VCHSRobots/EpicFMS/cad/MovingTarget/M21-MT-0001.SLDASM

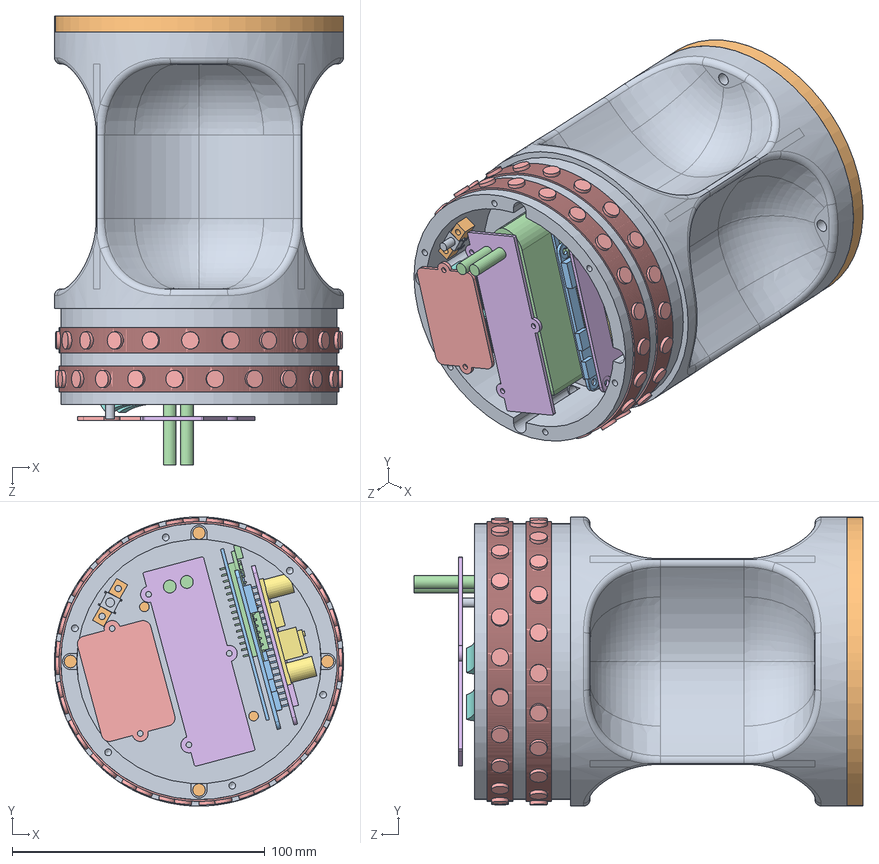
[picture p43: CAD file, 2021-10-06]
cad/MovingTarget/M21-MT-0001.SLDASM
114.4 x 114.3 x 177.5 mm
M21-MT-3002
M21-MT-3003
LipoBattery_1500mah_2S__Amazon
NeopixelRingSLDPRT x 2
M21-MT-7002
DCtoDC_Convertor_2Amp
RockerSwitch x 2
MicroPushButton
M21-MT-3006
ElegooBoard_Thin
ESP8266
