VCHSRobots/EpicFMS/cad/MovingTarget/M21-MT-0002.SLDASM

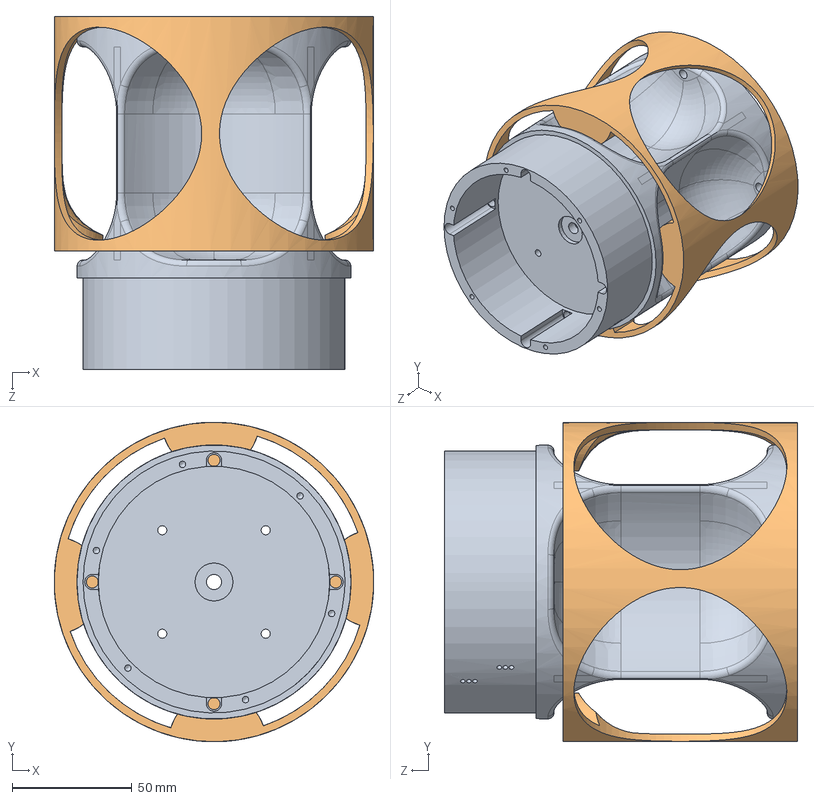
[picture p44: CAD file, 2021-10-06]
cad/MovingTarget/M21-MT-0002.SLDASM
133.3 x 133.3 x 147.3 mm
M21-MT-3002
M21-MT-3005
