VCHSRobots/EpicFMS/cad/CamerRingLEDs/M21-GP-3013.SLDPRT

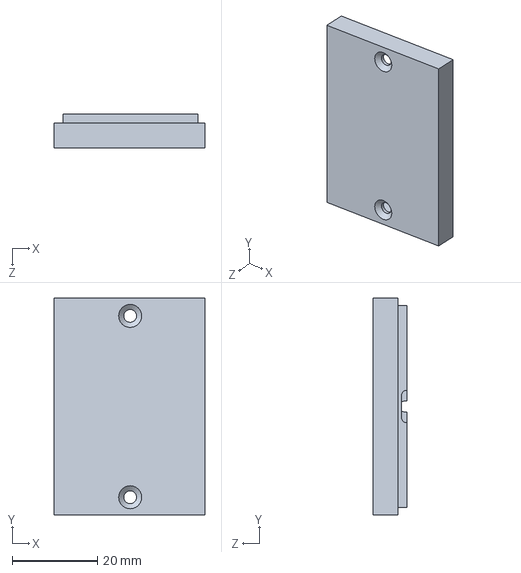
[picture p45: CAD file, 2021-11-01]
cad/CamerRingLEDs/M21-GP-3013.SLDPRT
35.2 x 50.8 x 7.87 mm
