VCHSRobots/EpicFMS/cad/DocTrash/TargetBoardForDiagram.SLDPRT

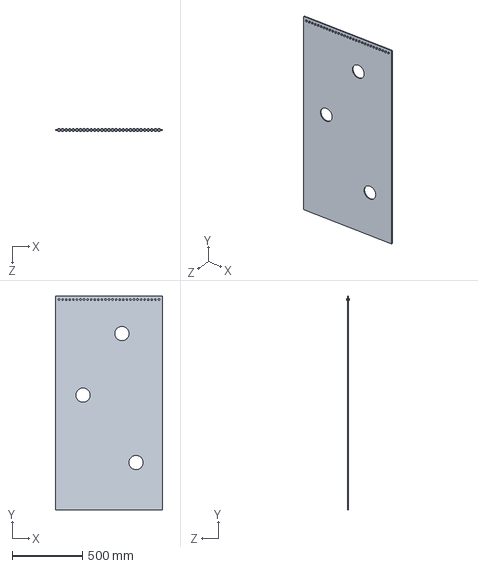
[picture p46: CAD file, 2021-10-06]
cad/DocTrash/TargetBoardForDiagram.SLDPRT
762.0 x 1524.0 x 19.0 mm
