VCHSRobots/EpicFMS/cad/DoorSliderTarget/M21-SL-3012.SLDPRT

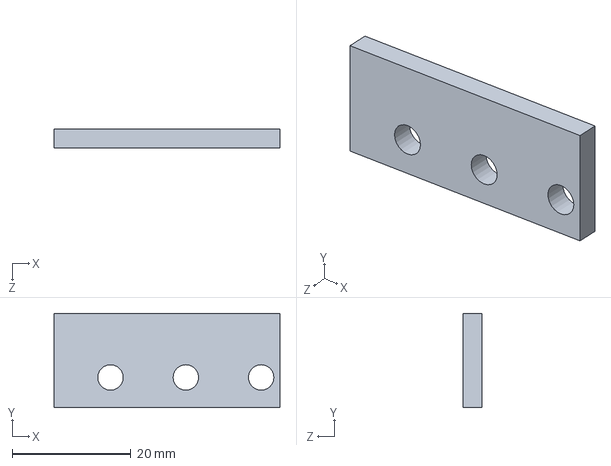
[picture p47: CAD file, 2021-10-22]
cad/DoorSliderTarget/M21-SL-3012.SLDPRT
38.1 x 15.9 x 3.17 mm
