VCHSRobots/EpicFMS/cad/MovingTarget/M21-MT-3010.SLDPRT

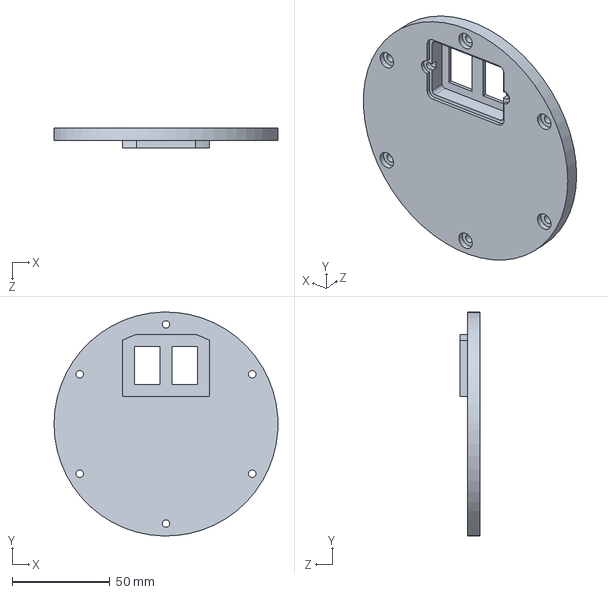
[picture p48: CAD file, 2021-10-29]
cad/MovingTarget/M21-MT-3010.SLDPRT
114.3 x 114.2 x 10.2 mm
