VCHSRobots/EpicFMS/cad/SupplierLib/DCtoDC_Convertor_eBoot_Mini_MP1584EN_Amazon.SLDPRT

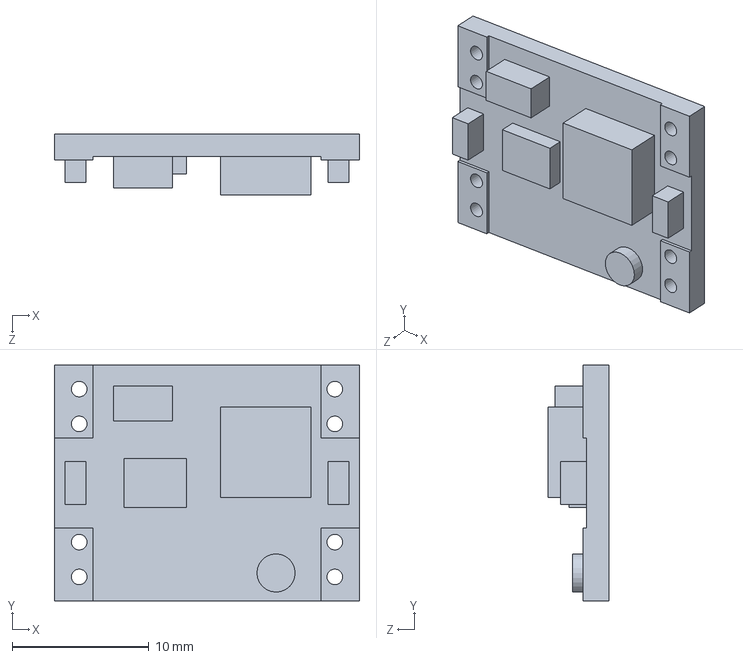
[picture p49: CAD file, 2021-11-01]
cad/SupplierLib/DCtoDC_Convertor_eBoot_Mini_MP1584EN_Amazon.SLDPRT
22.3 x 17.2 x 4.42 mm
