VCHSRobots/EpicFMS/cad/TestJigs/M21-GP-3002.SLDPRT

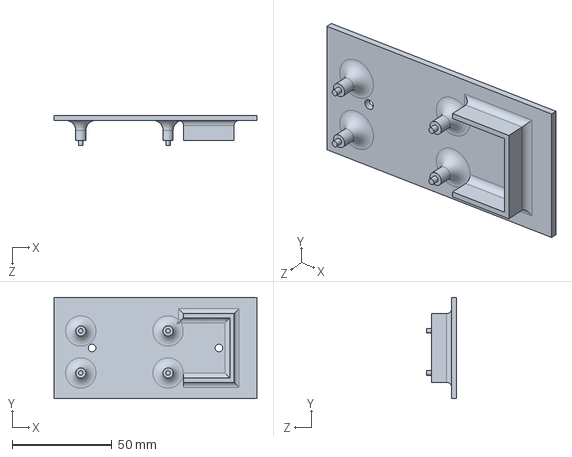
[picture p50: CAD file, 2021-10-07]
cad/TestJigs/M21-GP-3002.SLDPRT
101.6 x 50.8 x 15.2 mm
