VCHSRobots/EpicFMS/cad/BasketTarget/M21-HG-3004.SLDPRT

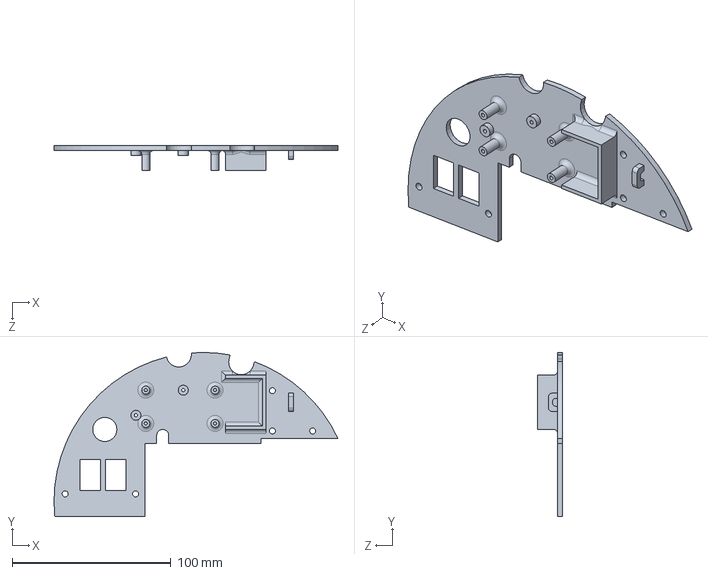
[picture p51: CAD file, 2021-10-07]
cad/BasketTarget/M21-HG-3004.SLDPRT
179.2 x 103.5 x 15.9 mm
