VCHSRobots/EpicFMS/cad/DocTrash/BasketForDiagram.SLDPRT

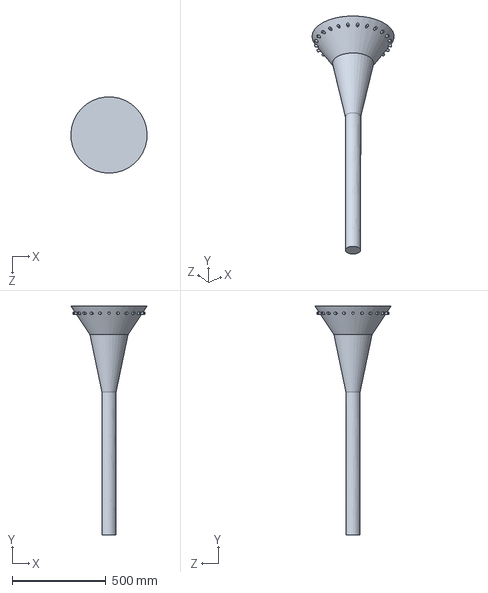
[picture p52: CAD file, 2021-10-06]
cad/DocTrash/BasketForDiagram.SLDPRT
406.0 x 1219.2 x 406.4 mm
