VCHSRobots/EpicFMS/cad/MovingTarget/M21-MT-3011.SLDPRT

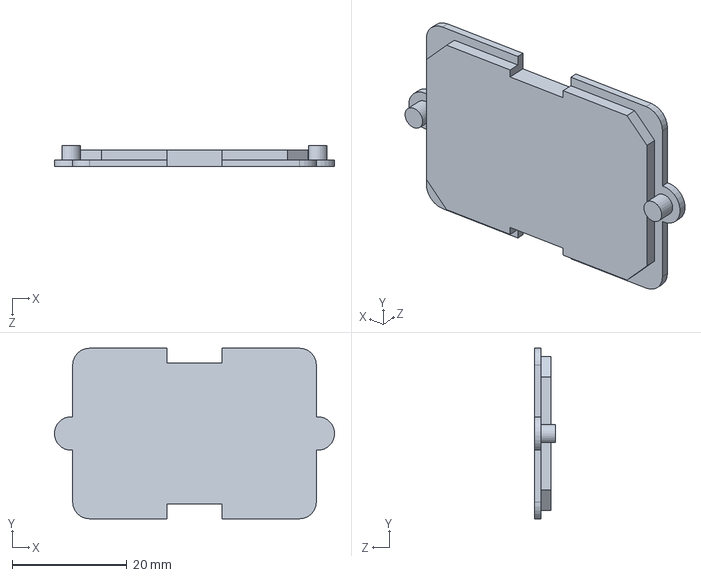
[picture p53: CAD file, 2021-10-29]
cad/MovingTarget/M21-MT-3011.SLDPRT
48.7 x 29.7 x 3.70 mm
