VCHSRobots/EpicFMS/cad/PCB_Models/M21-GP-7003.SLDPRT

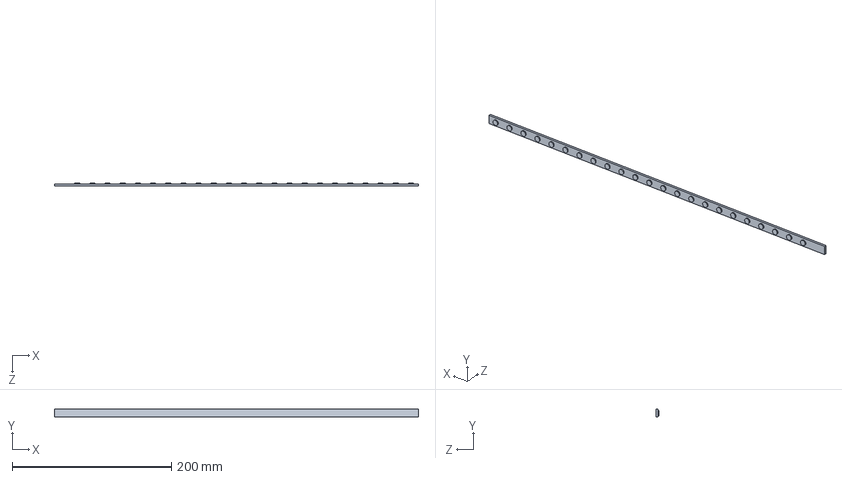
[picture p54: CAD file, 2021-10-09]
cad/PCB_Models/M21-GP-7003.SLDPRT
457.2 x 10.2 x 3.81 mm
