VCHSRobots/EpicFMS/cad/PowerSupplyBox/M21-GP-3008.SLDPRT

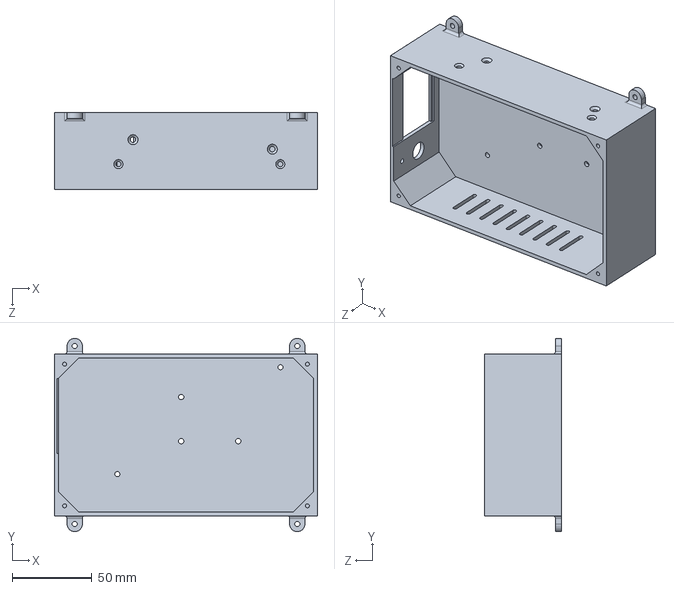
[picture p55: CAD file, 2021-10-20]
cad/PowerSupplyBox/M21-GP-3008.SLDPRT
165.1 x 121.4 x 48.3 mm
