VCHSRobots/EpicFMS/cad/SupplierLib/LipoBattery_1000mah_2S_Amazon.SLDPRT

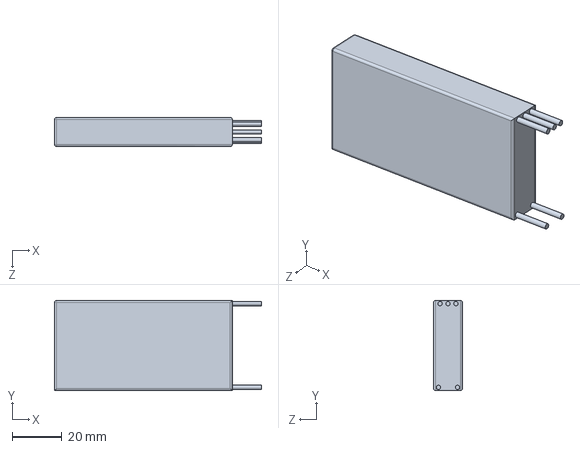
[picture p56: CAD file, 2021-10-27]
cad/SupplierLib/LipoBattery_1000mah_2S_Amazon.SLDPRT
82.8 x 36.1 x 11.7 mm
