VCHSRobots/EpicFMS/cad/TestJigs/M21-SL-3008.SLDPRT

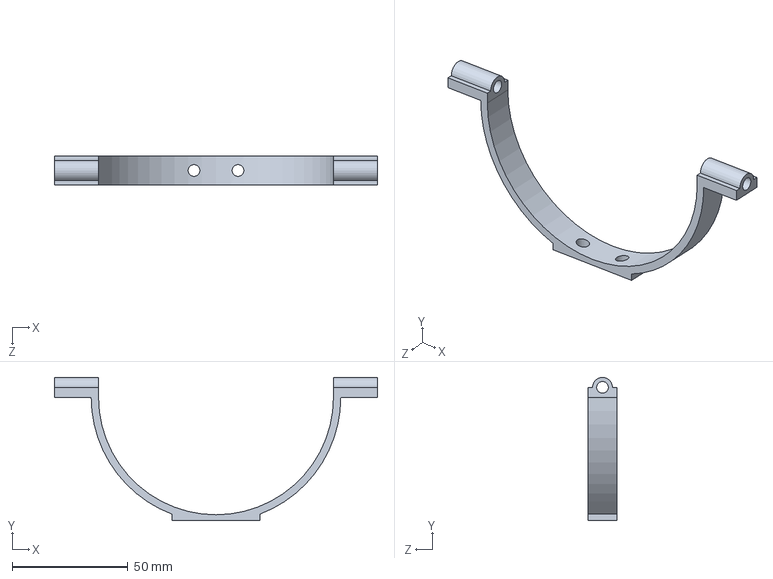
[picture p57: CAD file, 2021-10-06]
cad/TestJigs/M21-SL-3008.SLDPRT
139.7 x 62.0 x 12.7 mm
