VCHSRobots/EpicFMS/cad/BasketTarget/M21-HG-3005.SLDPRT

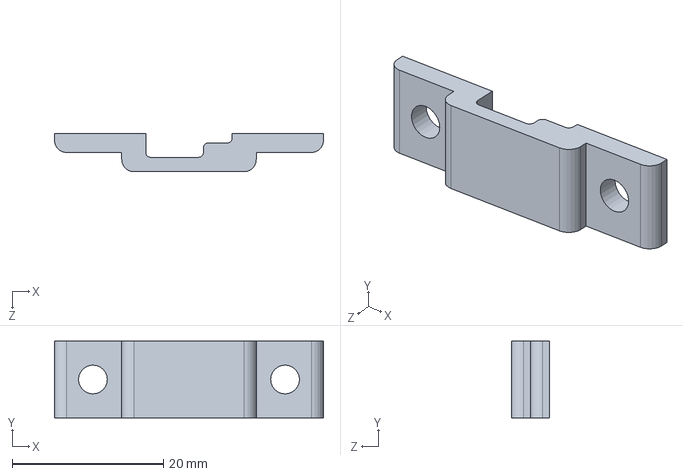
[picture p58: CAD file, 2021-10-07]
cad/BasketTarget/M21-HG-3005.SLDPRT
35.6 x 10.2 x 5.08 mm
