VCHSRobots/EpicFMS/cad/DocTrash/MovingTargetForDiagram.SLDPRT

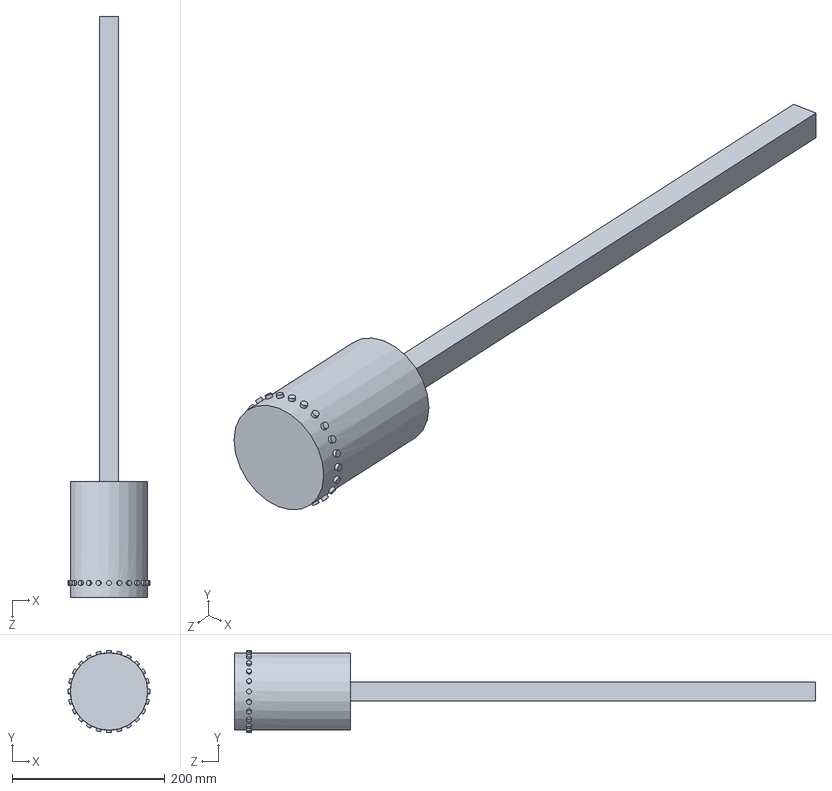
[picture p59: CAD file, 2021-10-06]
cad/DocTrash/MovingTargetForDiagram.SLDPRT
108.0 x 108.0 x 762.0 mm
