VCHSRobots/EpicFMS/cad/DoorSliderTarget/M21-SL-3009.SLDPRT

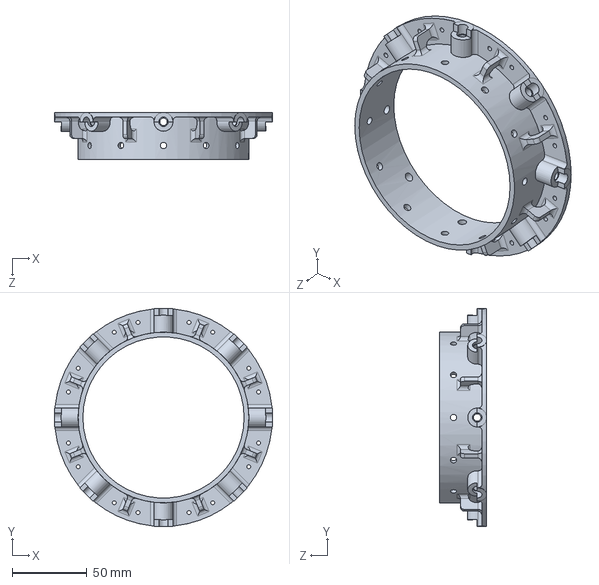
[picture p60: CAD file, 2021-10-09]
cad/DoorSliderTarget/M21-SL-3009.SLDPRT
146.2 x 146.2 x 31.8 mm
