VCHSRobots/EpicFMS/cad/PCB_Models/M21-GP-7002.SLDPRT

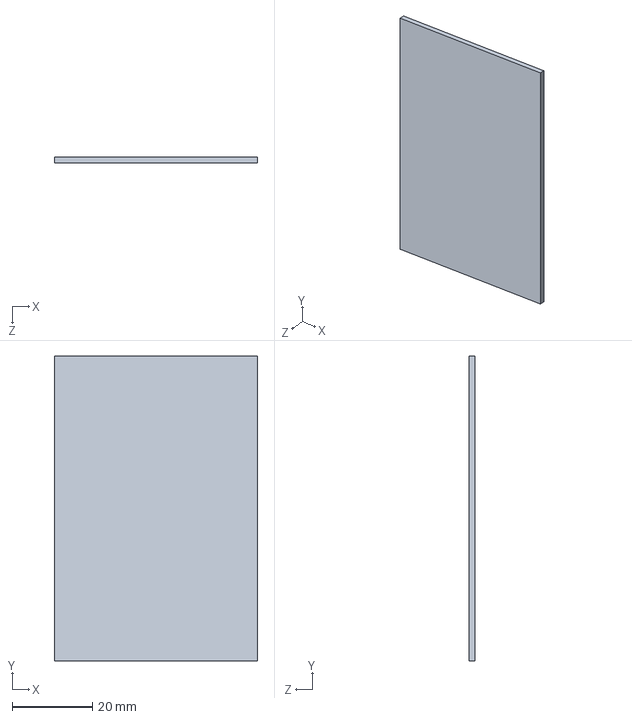
[picture p61: CAD file, 2021-10-09]
cad/PCB_Models/M21-GP-7002.SLDPRT
50.8 x 76.2 x 1.59 mm
