VCHSRobots/EpicFMS/cad/PowerSupplyBox/M21-GP-3009.SLDPRT

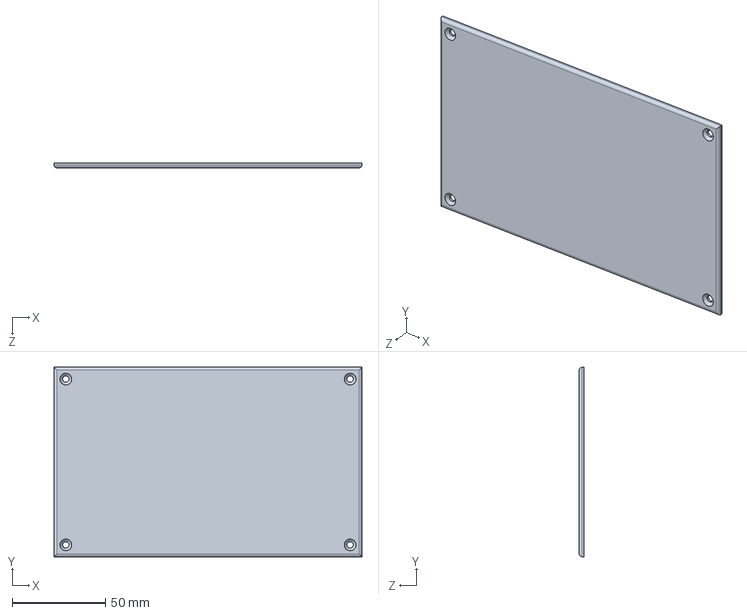
[picture p62: CAD file, 2021-10-20]
cad/PowerSupplyBox/M21-GP-3009.SLDPRT
165.1 x 101.6 x 2.54 mm
