VCHSRobots/EpicFMS/cad/SupplierLib/HeatSink_Digitkey.SLDPRT

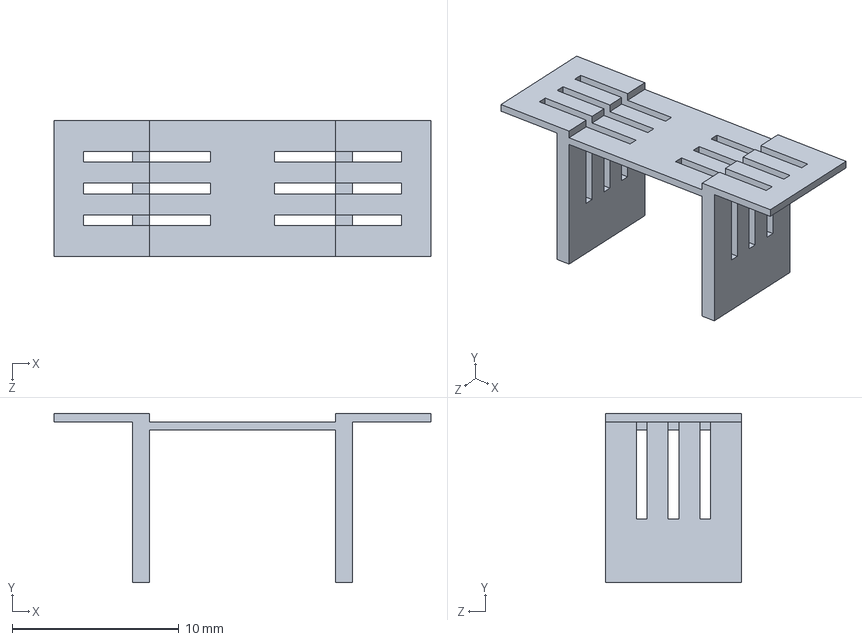
[picture p63: CAD file, 2021-10-27]
cad/SupplierLib/HeatSink_Digitkey.SLDPRT
22.6 x 10.2 x 8.13 mm
