VCHSRobots/EpicFMS/cad/TestJigs/M21-GP-3004.SLDPRT

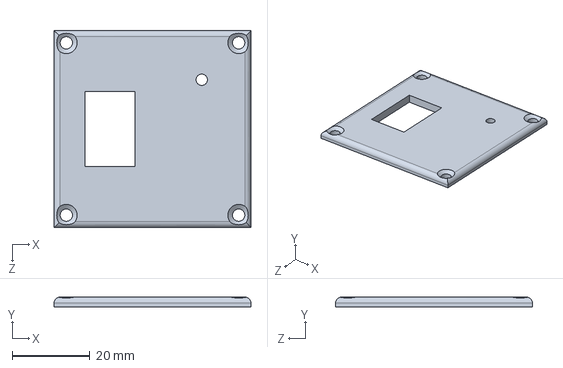
[picture p64: CAD file, 2021-10-06]
cad/TestJigs/M21-GP-3004.SLDPRT
50.8 x 2.54 x 50.8 mm
