VCHSRobots/EpicFMS/cad/BasketTarget/M21-HG-3001.SLDPRT

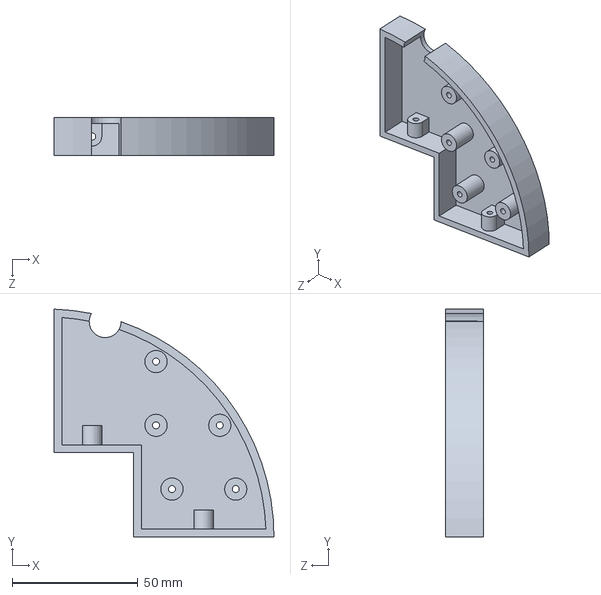
[picture p65: CAD file, 2021-10-06]
cad/BasketTarget/M21-HG-3001.SLDPRT
87.6 x 90.7 x 15.2 mm
