VCHSRobots/EpicFMS/cad/CamerRingLEDs/M21-GP-3012.SLDPRT

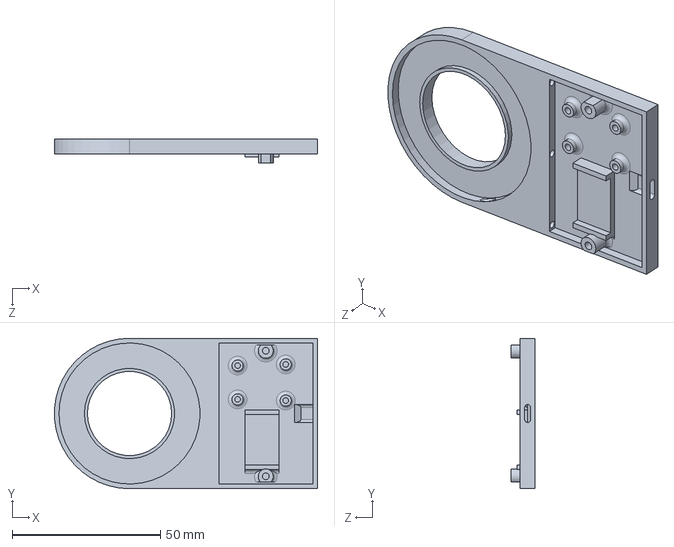
[picture p66: CAD file, 2021-11-01]
cad/CamerRingLEDs/M21-GP-3012.SLDPRT
88.8 x 50.8 x 8.26 mm
