VCHSRobots/EpicFMS/cad/DoorSliderTarget/M21-SL-3011.SLDPRT

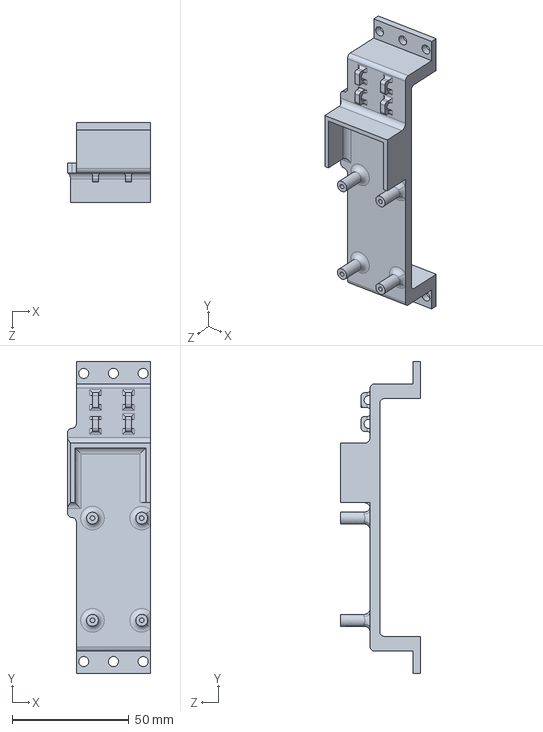
[picture p67: CAD file, 2021-10-09]
cad/DoorSliderTarget/M21-SL-3011.SLDPRT
35.6 x 133.4 x 34.3 mm
