VCHSRobots/EpicFMS/cad/SupplierLib/JST_XH_6Pin_Jack.SLDPRT

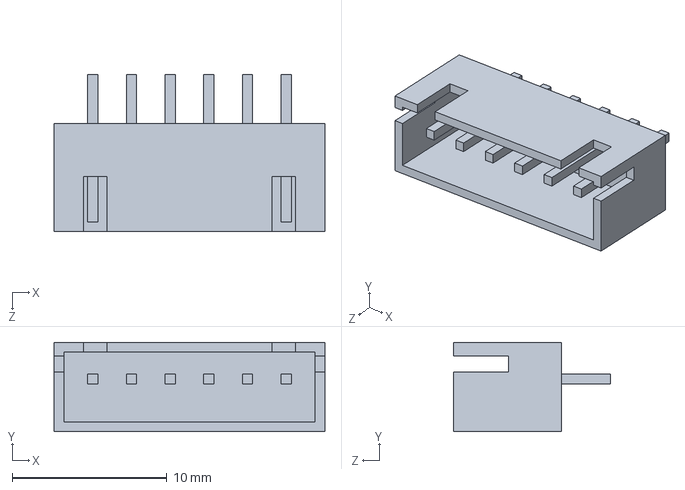
[picture p68: CAD file, 2021-10-27]
cad/SupplierLib/JST_XH_6Pin_Jack.SLDPRT
17.5 x 5.77 x 10.2 mm
