VCHSRobots/EpicFMS/cad/TestJigs/M21-GP-3003.SLDPRT

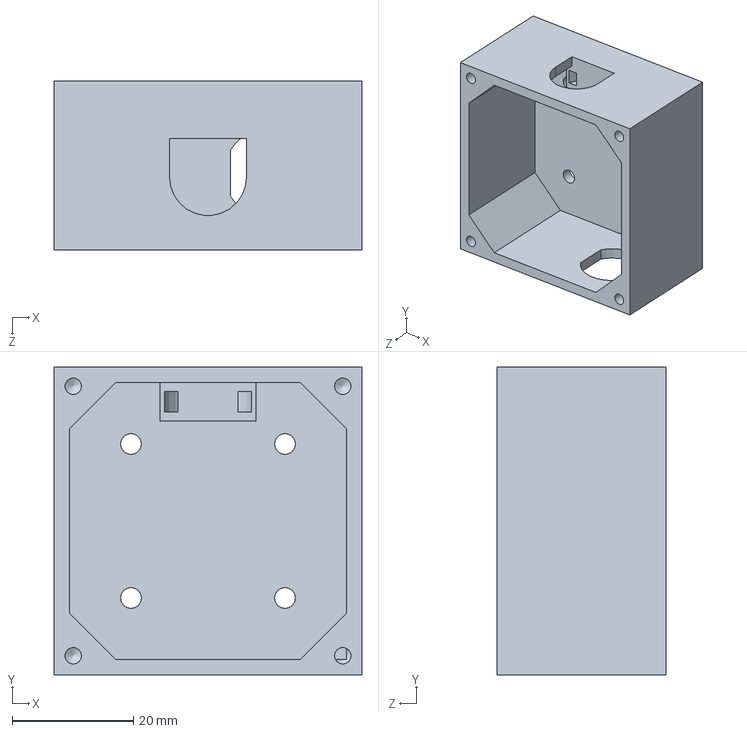
[picture p69: CAD file, 2021-10-05]
cad/TestJigs/M21-GP-3003.SLDPRT
50.8 x 50.8 x 27.9 mm
