VCHSRobots/EpicFMS/cad/BasketTarget/M21-HG-7001.SLDPRT

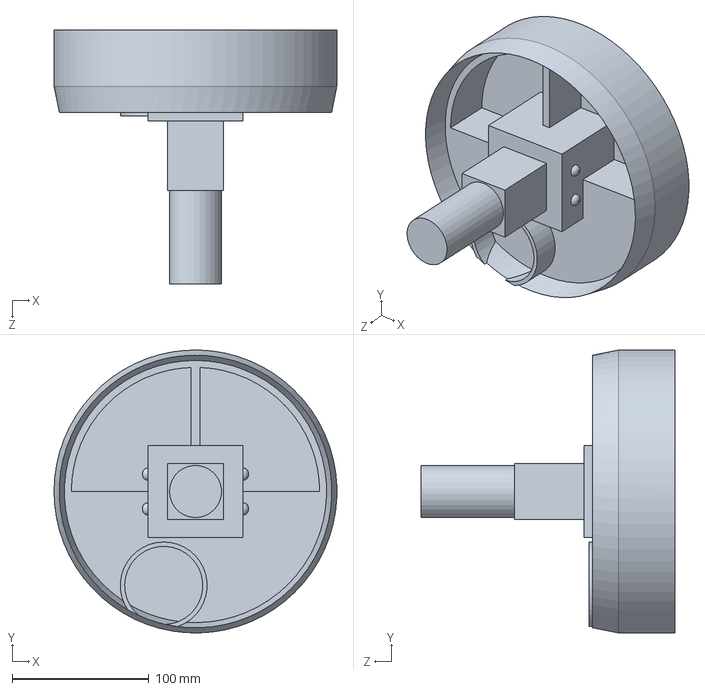
[picture p70: CAD file, 2021-10-06]
cad/BasketTarget/M21-HG-7001.SLDPRT
207.0 x 207.0 x 186.1 mm
