VCHSRobots/EpicFMS/cad/CamerRingLEDs/M21-GP-3011.SLDPRT

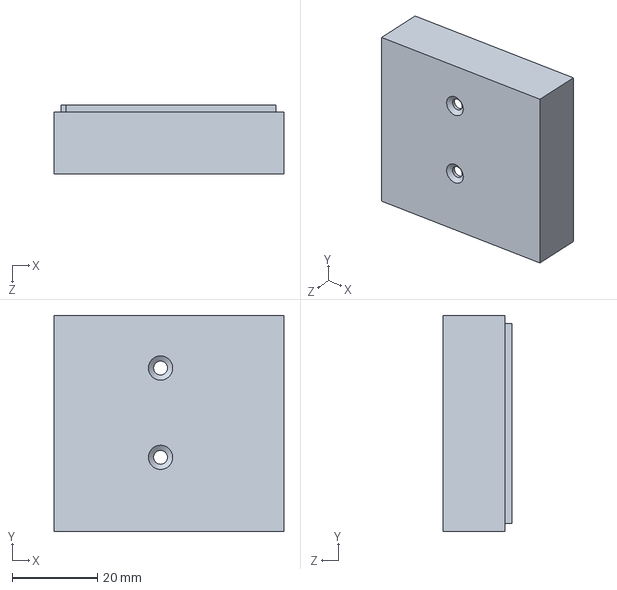
[picture p71: CAD file, 2021-10-22]
cad/CamerRingLEDs/M21-GP-3011.SLDPRT
54.0 x 50.8 x 16.2 mm
