VCHSRobots/EpicFMS/cad/DoorSliderTarget/M21-SL-3006.SLDPRT

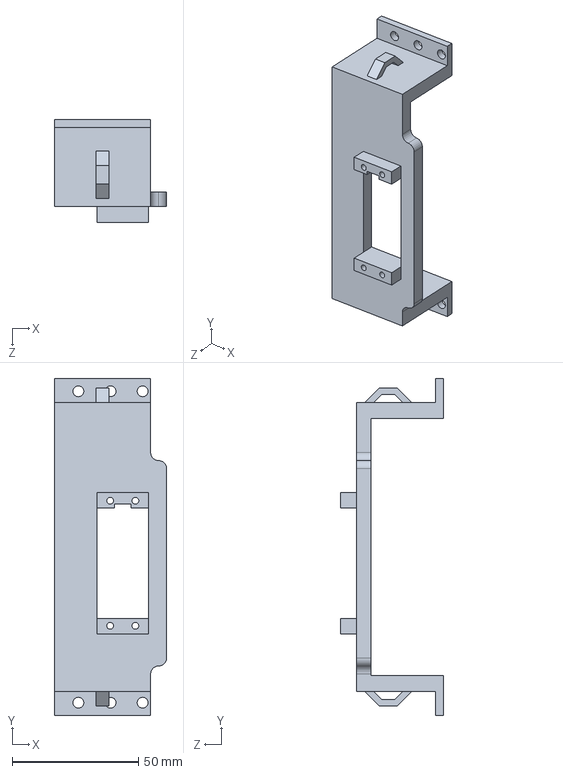
[picture p72: CAD file, 2021-10-09]
cad/DoorSliderTarget/M21-SL-3006.SLDPRT
44.4 x 133.4 x 40.6 mm
