VCHSRobots/EpicFMS/cad/MovingTarget/M21-MT-3009.SLDPRT

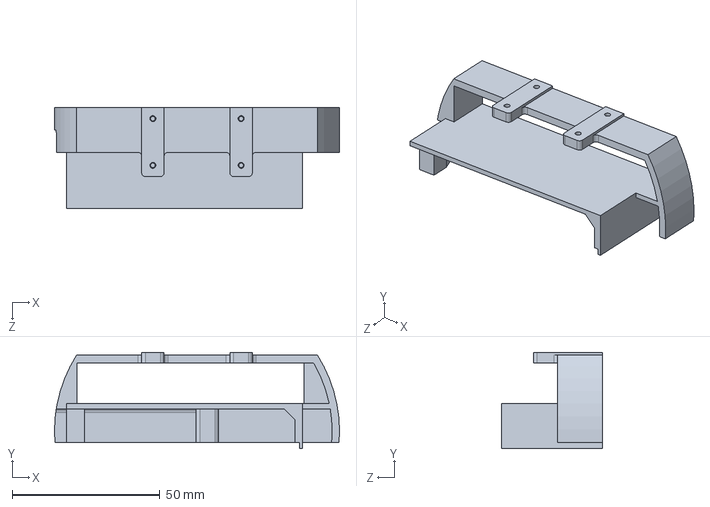
[picture p73: CAD file, 2021-10-29]
cad/MovingTarget/M21-MT-3009.SLDPRT
96.5 x 32.5 x 34.3 mm
