VCHSRobots/EpicFMS/cad/PCB_Models/M21-GP-7001.SLDPRT

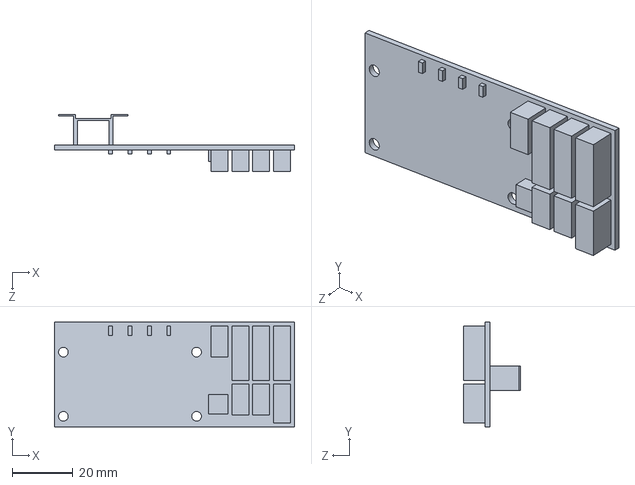
[picture p74: CAD file, 2021-10-06]
cad/PCB_Models/M21-GP-7001.SLDPRT
78.7 x 34.3 x 18.9 mm
