VCHSRobots/EpicFMS/cad/SupplierLib/JST_XH_4Pin_Jack.SLDPRT

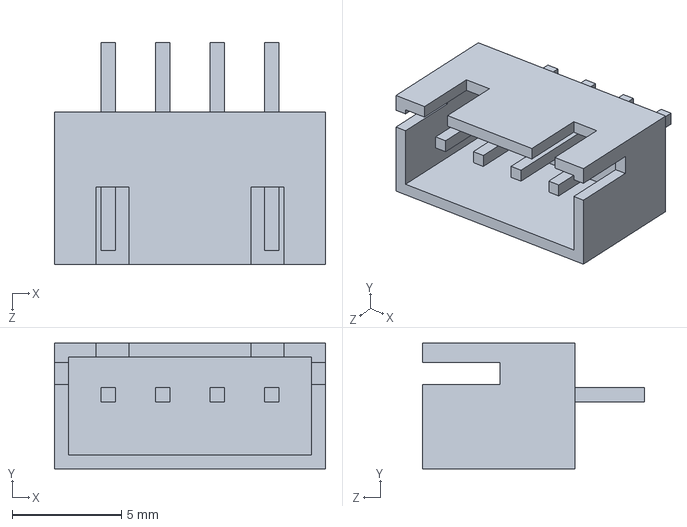
[picture p75: CAD file, 2021-10-27]
cad/SupplierLib/JST_XH_4Pin_Jack.SLDPRT
12.4 x 5.77 x 10.2 mm
