VCHSRobots/EpicFMS/cad/TestJigs/M21-GP-3007.SLDPRT

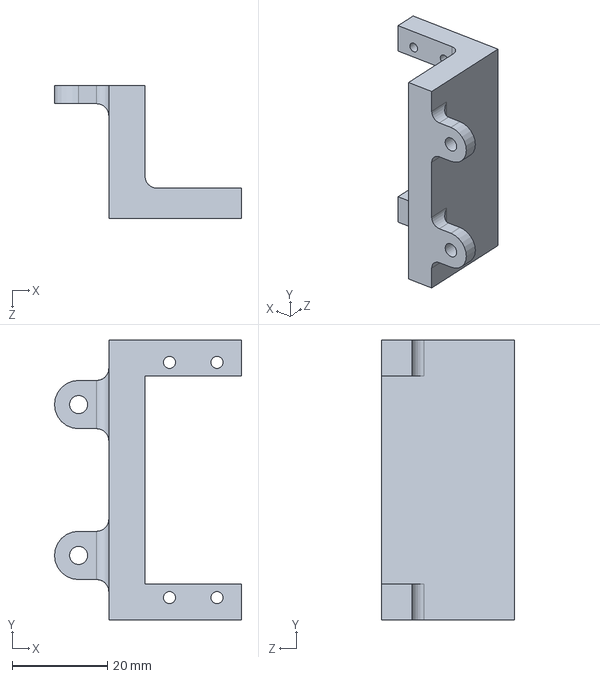
[picture p76: CAD file, 2021-10-05]
cad/TestJigs/M21-GP-3007.SLDPRT
39.4 x 58.9 x 27.9 mm
