VCHSRobots/EpicFMS/cad/BasketTarget/M21-HG-3003.SLDPRT

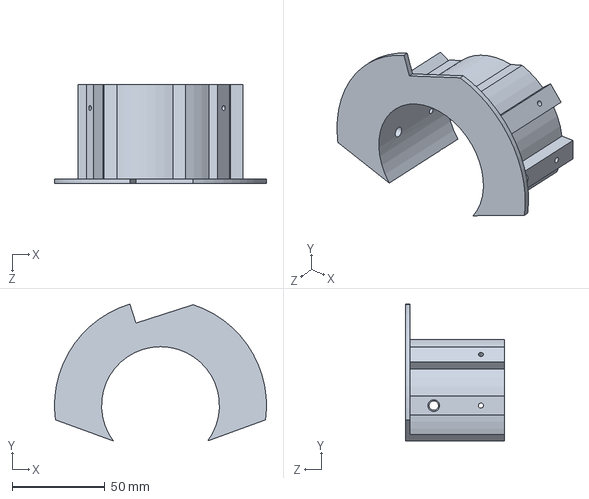
[picture p77: CAD file, 2021-10-06]
cad/BasketTarget/M21-HG-3003.SLDPRT
114.3 x 73.8 x 53.3 mm
