VCHSRobots/EpicFMS/cad/CamerRingLEDs/M21-GP-7004.SLDPRT

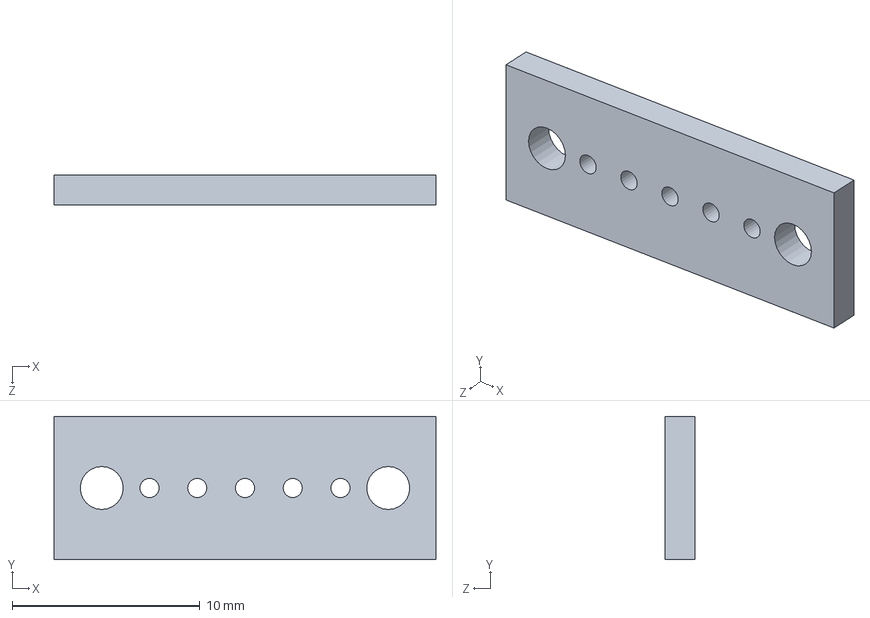
[picture p78: CAD file, 2021-10-18]
cad/CamerRingLEDs/M21-GP-7004.SLDPRT
20.3 x 7.62 x 1.59 mm
