VCHSRobots/EpicFMS/cad/DoorSliderTarget/M21-SL-6002.SLDPRT

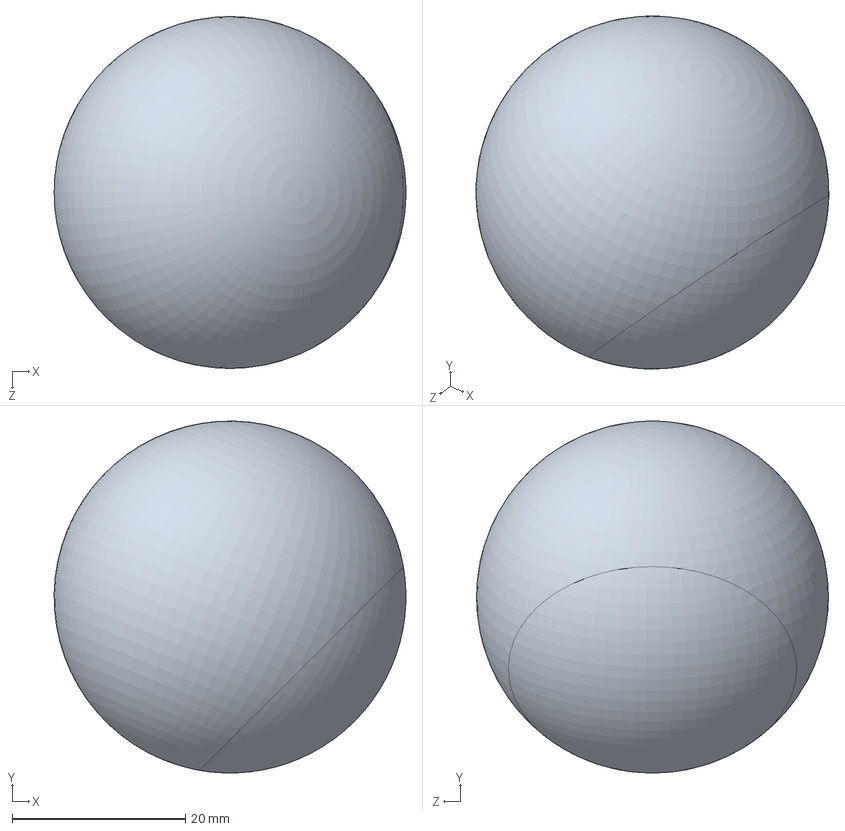
[picture p79: CAD file, 2021-10-06]
cad/DoorSliderTarget/M21-SL-6002.SLDPRT
40.6 x 40.6 x 40.6 mm
