VCHSRobots/EpicFMS/cad/SupplierLib/LED_Ring_16_Adafruit.SLDPRT

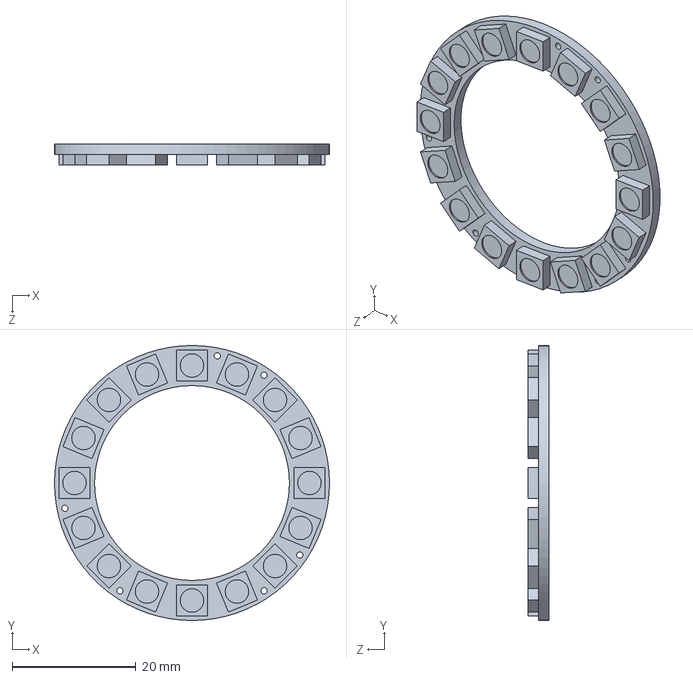
[picture p80: CAD file, 2021-10-18]
cad/SupplierLib/LED_Ring_16_Adafruit.SLDPRT
44.5 x 44.5 x 3.35 mm
