VCHSRobots/EpicFMS/cad/BasketTarget/M21-HG-7002.SLDPRT

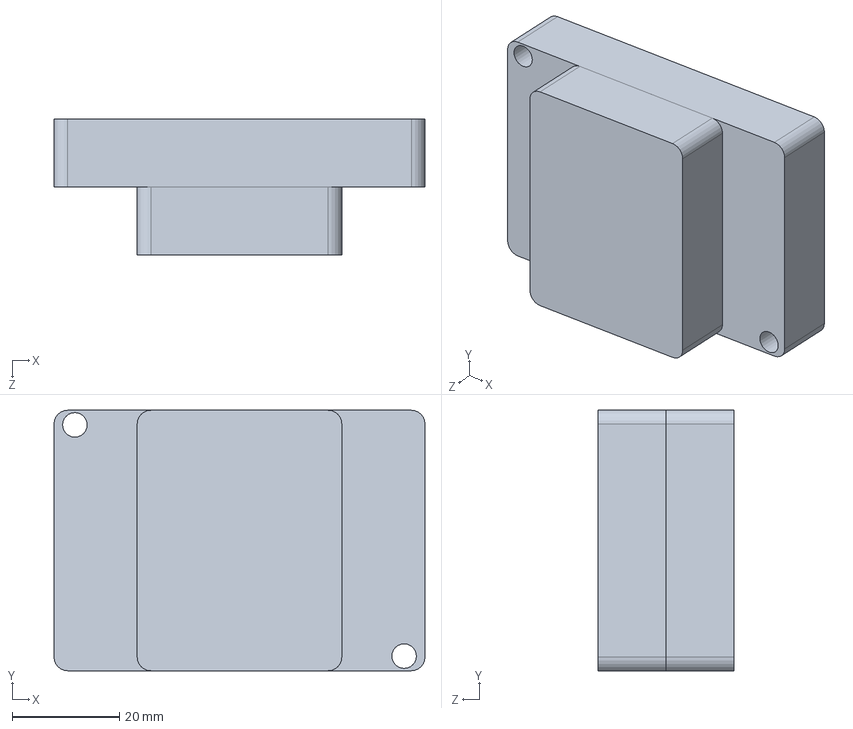
[picture p81: CAD file, 2021-10-06]
cad/BasketTarget/M21-HG-7002.SLDPRT
69.1 x 48.5 x 25.4 mm
