VCHSRobots/EpicFMS/cad/CamerRingLEDs/M21-GP-3010.SLDPRT

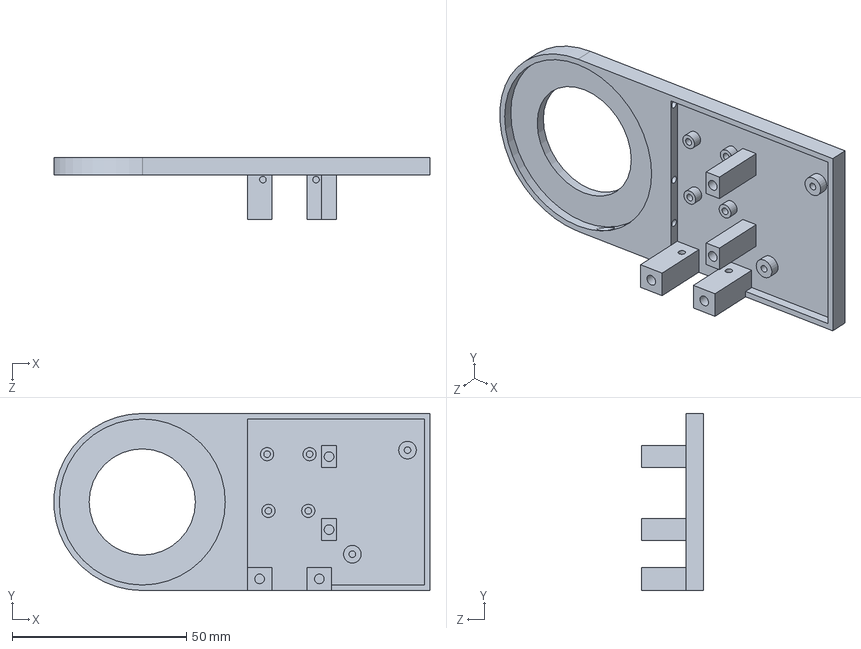
[picture p82: CAD file, 2021-10-18]
cad/CamerRingLEDs/M21-GP-3010.SLDPRT
107.9 x 50.8 x 17.8 mm
