VCHSRobots/EpicFMS/cad/SupplierLib/Trinket_M0_Adafruit.SLDPRT

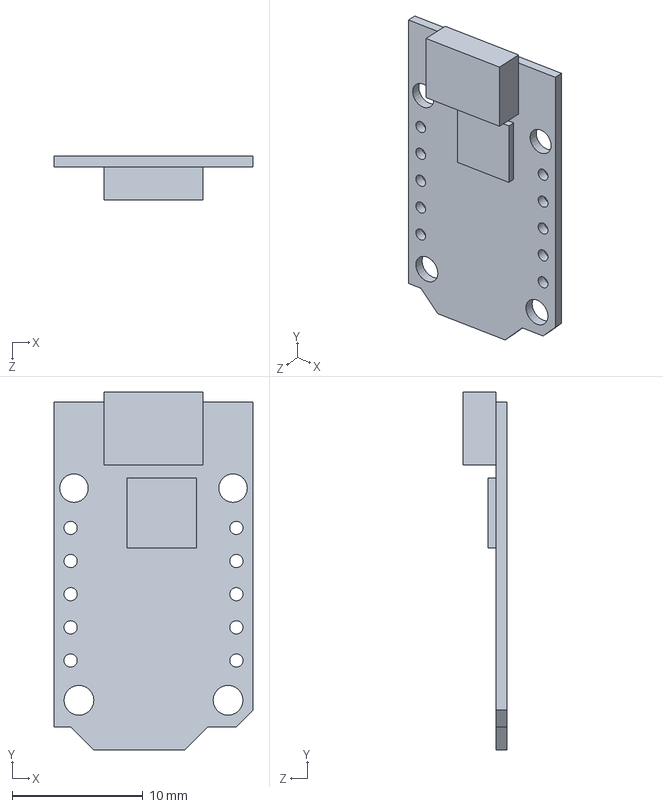
[picture p83: CAD file, 2021-10-18]
cad/SupplierLib/Trinket_M0_Adafruit.SLDPRT
15.2 x 27.4 x 3.37 mm
