VCHSRobots/EpicFMS/cad/TestJigs/M21-GP-3001.SLDPRT

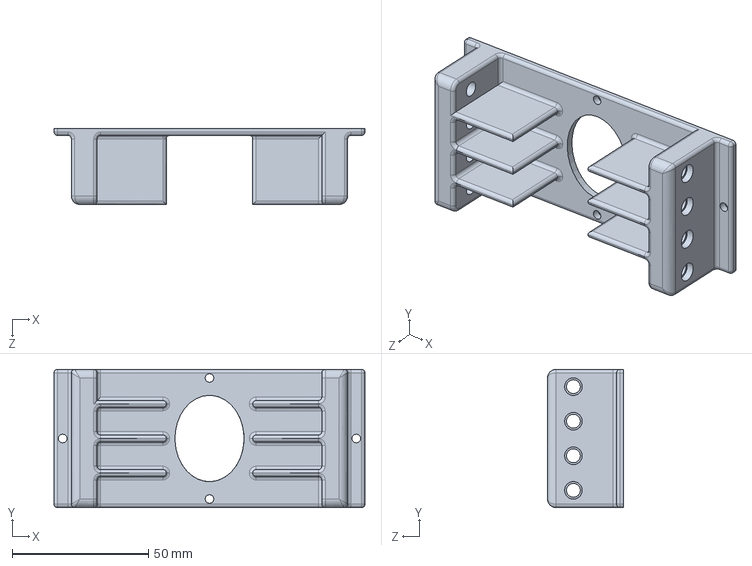
[picture p84: CAD file, 2021-10-05]
cad/TestJigs/M21-GP-3001.SLDPRT
114.3 x 50.8 x 27.9 mm
