VCHSRobots/EpicFMS/cad/BasketTarget/M21-HG-3002.SLDPRT

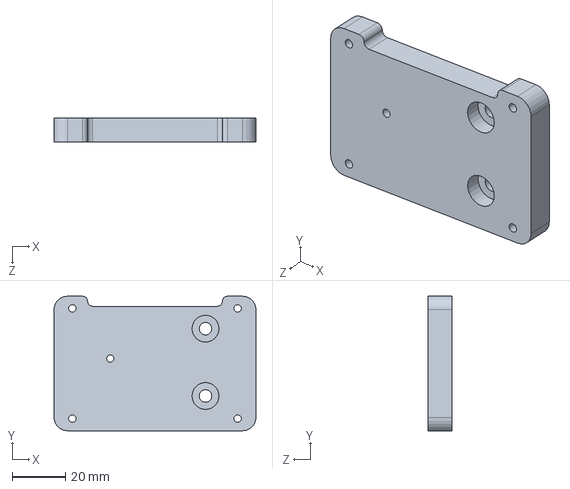
[picture p85: CAD file, 2021-10-06]
cad/BasketTarget/M21-HG-3002.SLDPRT
76.2 x 50.8 x 8.89 mm
