VCHSRobots/EpicFMS/cad/MovingTarget/M21-MT-7003.SLDPRT

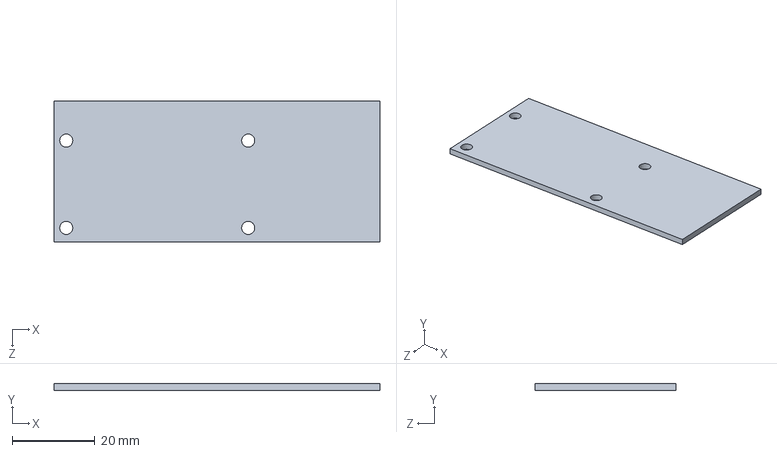
[picture p86: CAD file, 2021-10-27]
cad/MovingTarget/M21-MT-7003.SLDPRT
78.7 x 1.59 x 34.1 mm
