VCHSRobots/EpicFMS/cad/SupplierLib/JST_XH_3Pin_Jack.SLDPRT

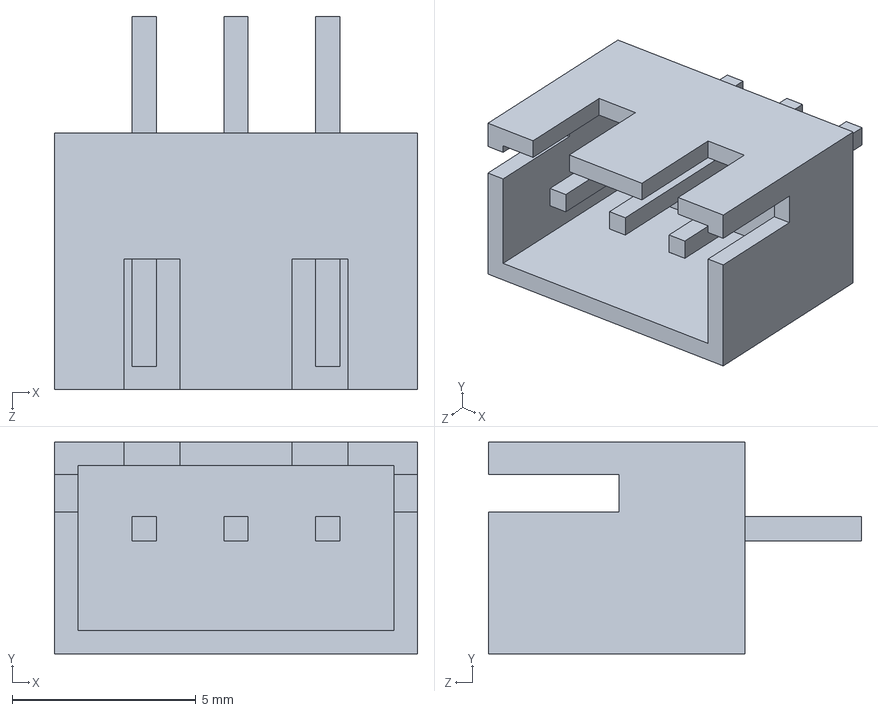
[picture p87: CAD file, 2021-10-18]
cad/SupplierLib/JST_XH_3Pin_Jack.SLDPRT
9.88 x 5.77 x 10.2 mm
