VCHSRobots/EpicFMS/cad/TestJigs/M21-GP-3005.SLDPRT

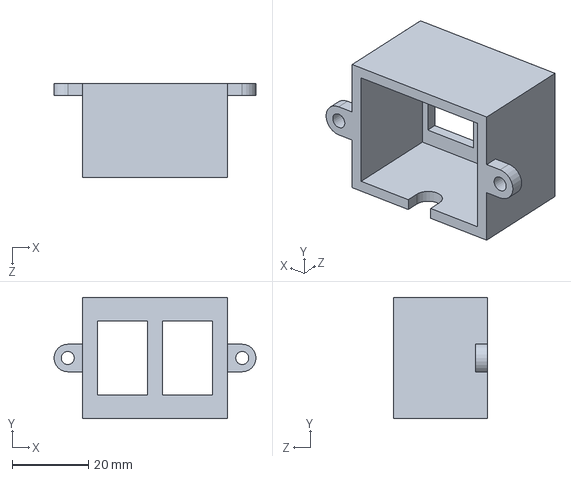
[picture p88: CAD file, 2021-10-05]
cad/TestJigs/M21-GP-3005.SLDPRT
53.0 x 31.8 x 24.8 mm
