VCHSRobots/EpicFMS/cad/DoorSliderTarget/M21-SL-3007.SLDPRT

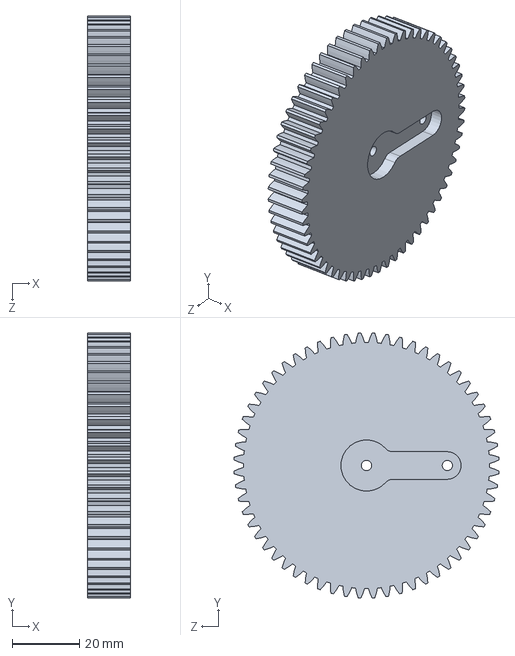
[picture p89: CAD file, 2021-10-06]
cad/DoorSliderTarget/M21-SL-3007.SLDPRT
12.7 x 78.7 x 78.7 mm
