VCHSRobots/EpicFMS/cad/MovingTarget/M21-MT-3004.SLDPRT

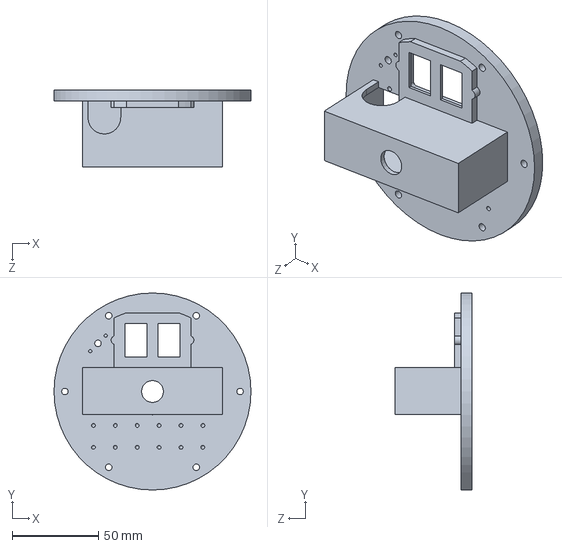
[picture p90: CAD file, 2021-10-06]
cad/MovingTarget/M21-MT-3004.SLDPRT
114.3 x 114.3 x 44.5 mm
