VCHSRobots/EpicFMS/cad/SupplierLib/AC_PowerSupply_Amazon_12v_5Amps.SLDPRT

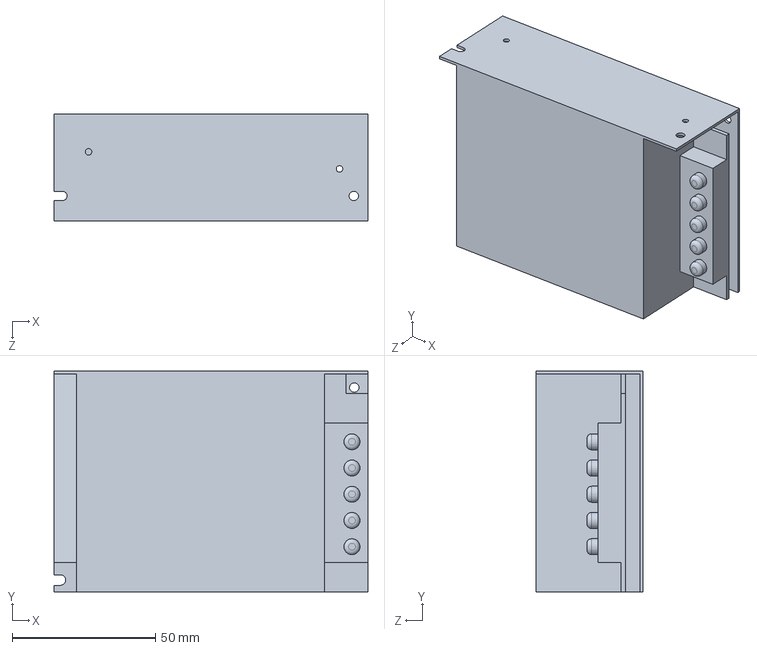
[picture p91: CAD file, 2021-10-16]
cad/SupplierLib/AC_PowerSupply_Amazon_12v_5Amps.SLDPRT
109.5 x 77.0 x 37.3 mm
