VCHSRobots/EpicFMS/cad/DoorSliderTarget/M21-SL-6001.SLDPRT

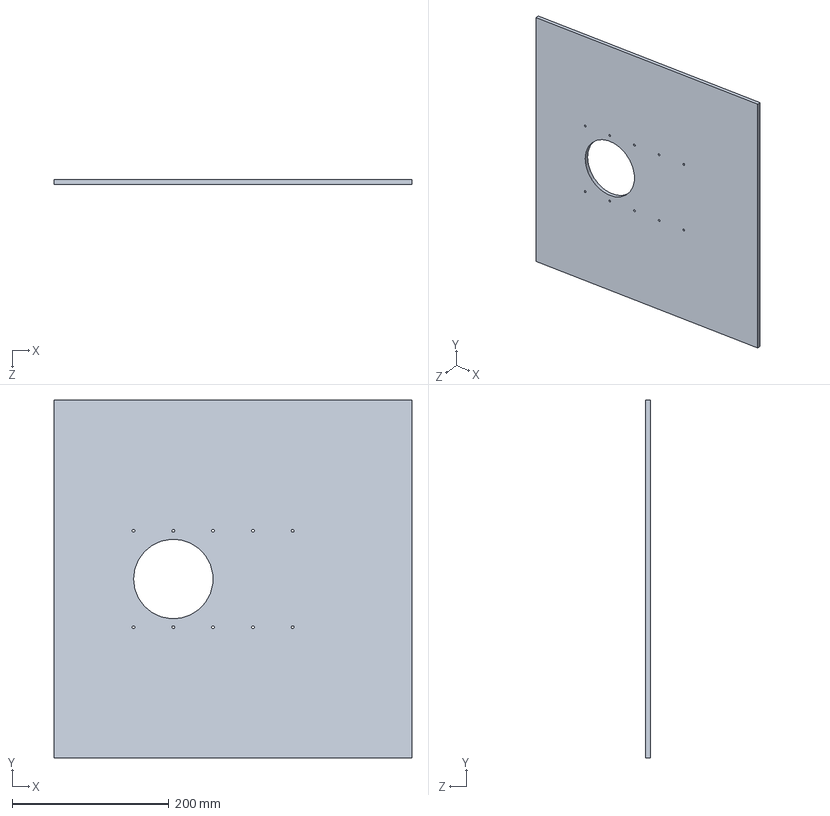
[picture p92: CAD file, 2021-10-06]
cad/DoorSliderTarget/M21-SL-6001.SLDPRT
457.2 x 457.2 x 6.35 mm
