VCHSRobots/EpicFMS/cad/MovingTarget/M21-MT-3008.SLDPRT

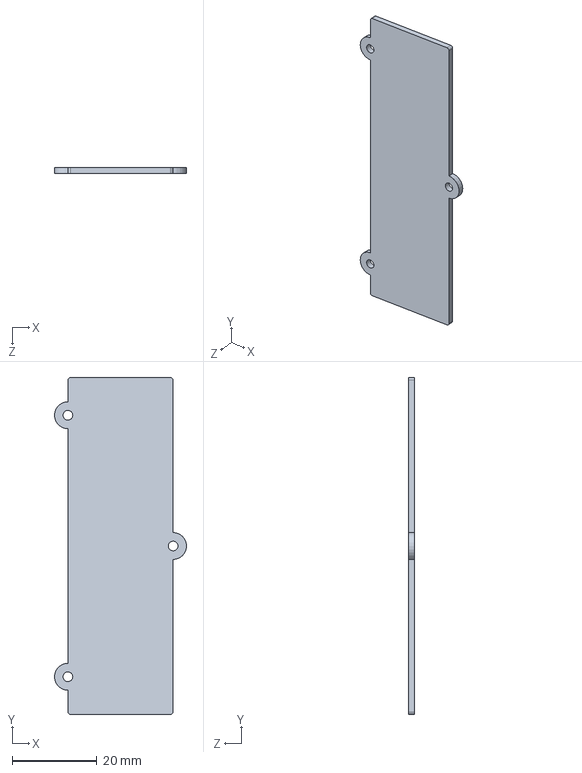
[picture p93: CAD file, 2021-10-06]
cad/MovingTarget/M21-MT-3008.SLDPRT
31.1 x 79.4 x 1.52 mm
