VCHSRobots/EpicFMS/cad/SupplierLib/AC_PowerSocketWithSwitchAndFuse.SLDPRT

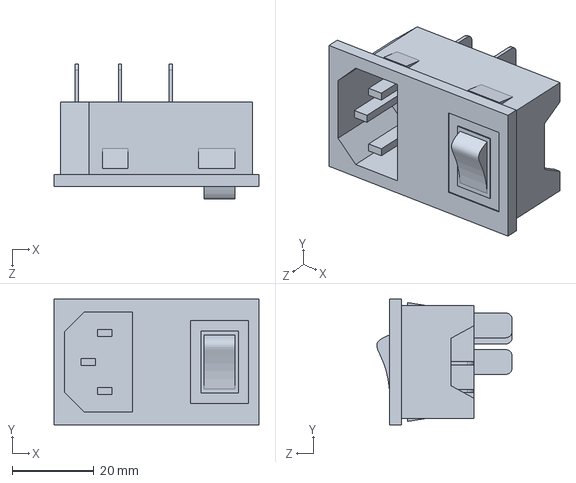
[picture p94: CAD file, 2021-10-16]
cad/SupplierLib/AC_PowerSocketWithSwitchAndFuse.SLDPRT
50.3 x 30.9 x 33.2 mm
