VCHSRobots/EpicFMS/cad/DoorSliderTarget/M21-SL-3002.SLDPRT

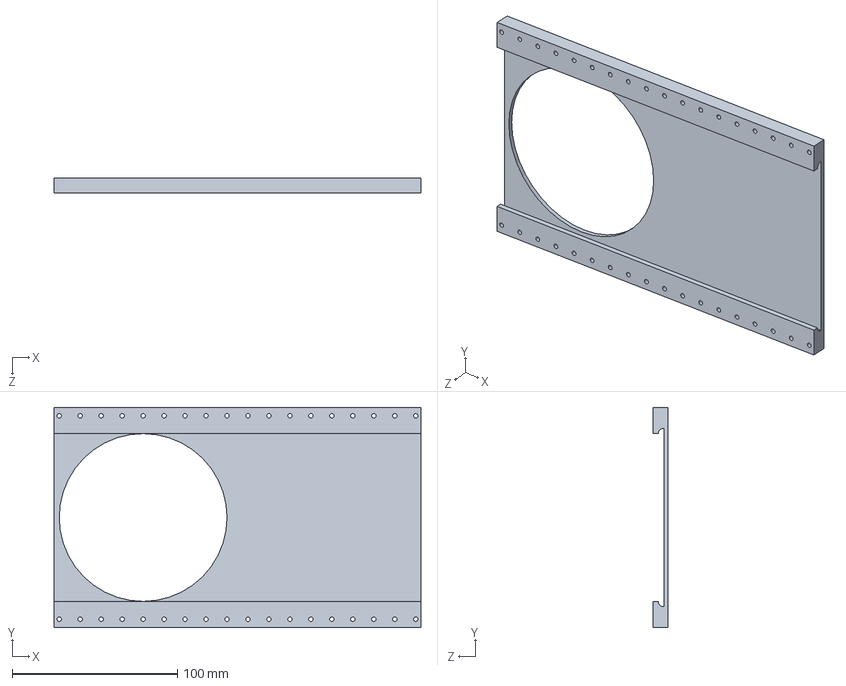
[picture p95: CAD file, 2021-10-06]
cad/DoorSliderTarget/M21-SL-3002.SLDPRT
222.2 x 133.4 x 9.02 mm
