VCHSRobots/EpicFMS/cad/MovingTarget/M21-MT-3005.SLDPRT

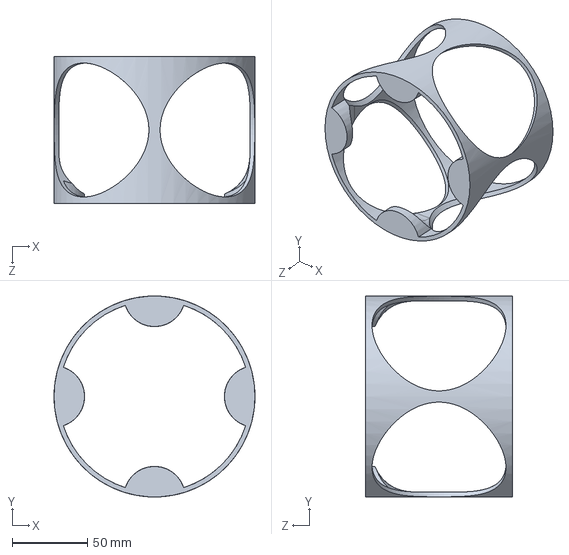
[picture p96: CAD file, 2021-10-06]
cad/MovingTarget/M21-MT-3005.SLDPRT
133.4 x 133.1 x 97.8 mm
