VCHSRobots/EpicFMS/cad/SupplierLib/Jack_5p5mm_2p5mm.SLDPRT

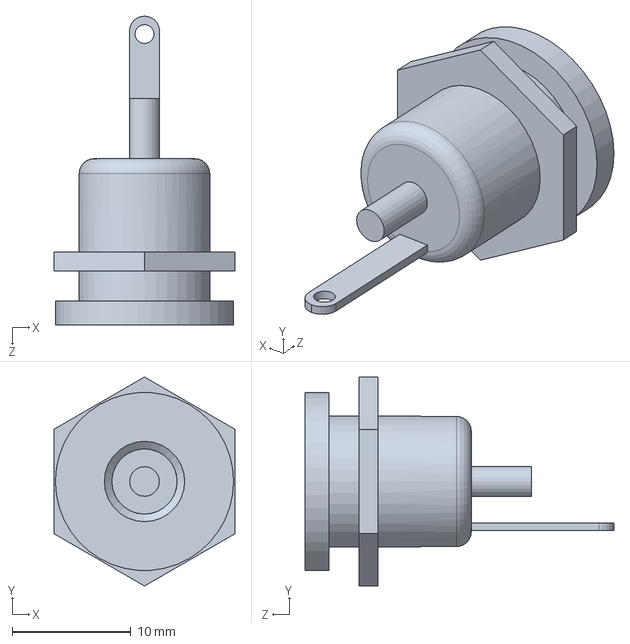
[picture p97: CAD file, 2021-10-16]
cad/SupplierLib/Jack_5p5mm_2p5mm.SLDPRT
15.2 x 17.6 x 26.0 mm
