VCHSRobots/EpicFMS/cad/DoorSliderTarget/M21-SL-3004..SLDPRT

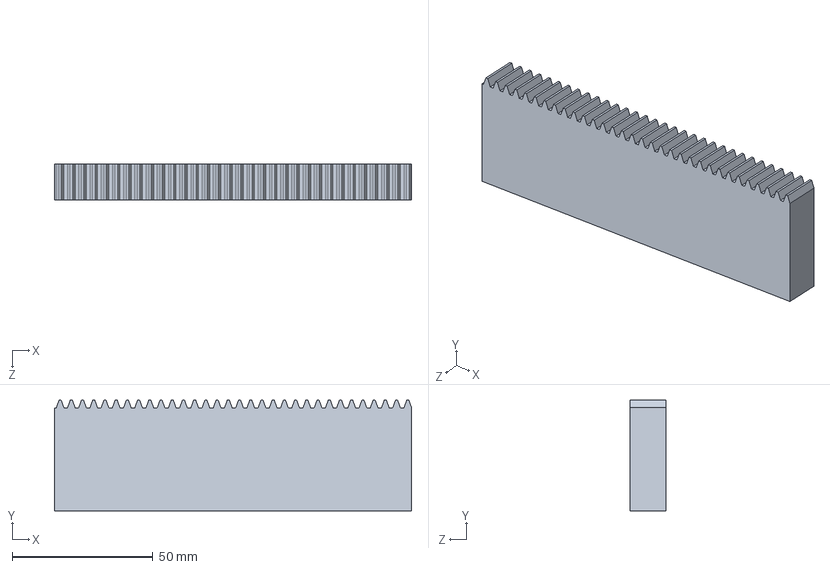
[picture p98: CAD file, 2021-10-06]
cad/DoorSliderTarget/M21-SL-3004..SLDPRT
127.0 x 39.4 x 12.7 mm
