VCHSRobots/EpicFMS/cad/MovingTarget/M21-MT-3003.SLDPRT

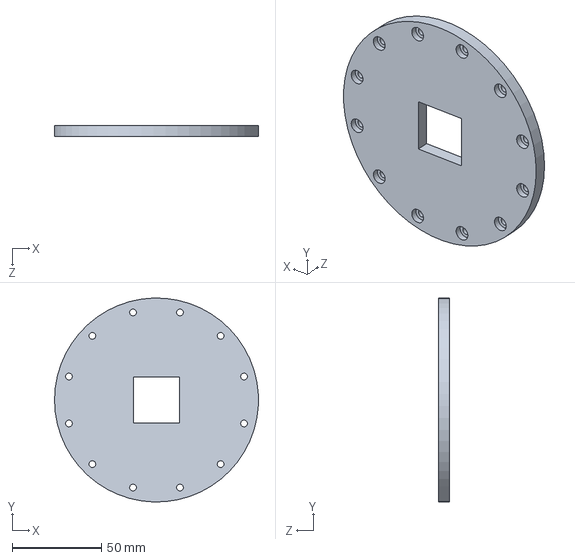
[picture p99: CAD file, 2021-10-06]
cad/MovingTarget/M21-MT-3003.SLDPRT
114.3 x 114.2 x 6.35 mm
