VCHSRobots/EpicFMS/cad/SupplierLib/DCtoDC_Convertor_2Amp.SLDPRT

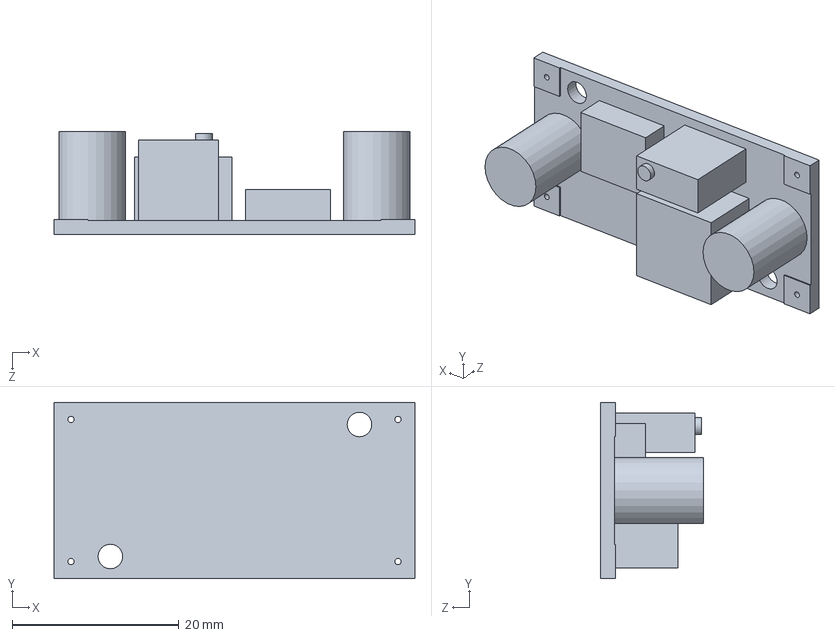
[picture p100: CAD file, 2021-10-07]
cad/SupplierLib/DCtoDC_Convertor_2Amp.SLDPRT
43.3 x 21.1 x 12.3 mm
