VCHSRobots/EpicFMS/cad/DoorSliderTarget/M21-SL-3010.SLDPRT

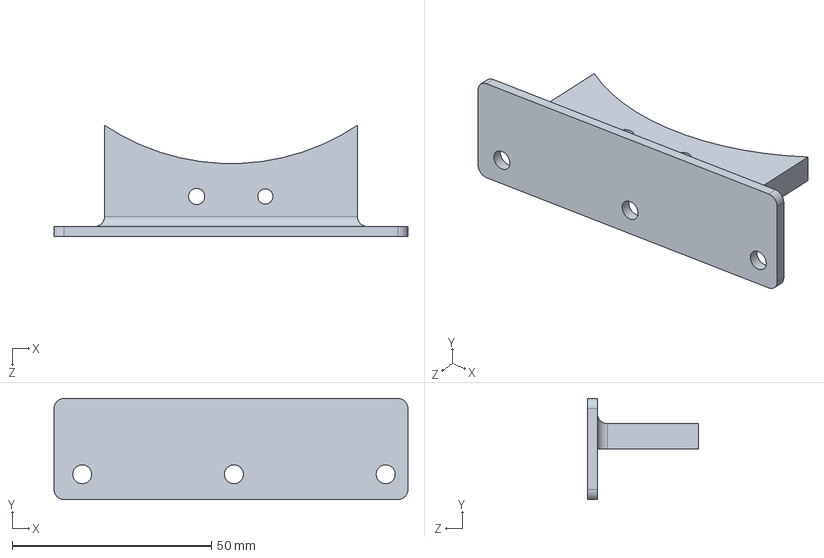
[picture p101: CAD file, 2021-10-06]
cad/DoorSliderTarget/M21-SL-3010.SLDPRT
88.9 x 25.4 x 28.0 mm
