VCHSRobots/EpicFMS/cad/SupplierLib/ElegooBoard_Medium.SLDPRT

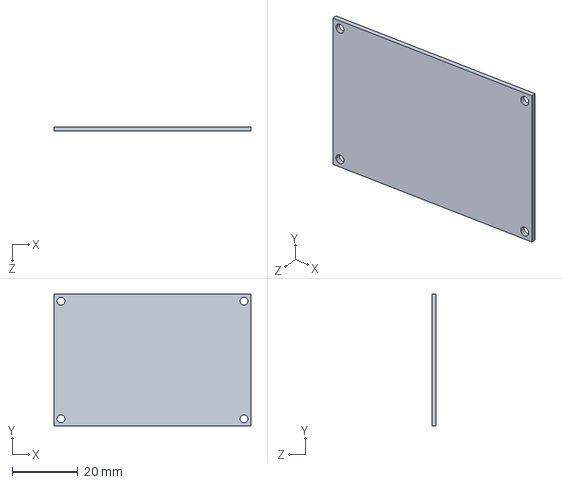
[picture p102: CAD file, 2021-10-06]
cad/SupplierLib/ElegooBoard_Medium.SLDPRT
60.1 x 40.2 x 1.27 mm
