VCHSRobots/EpicFMS/cad/DoorSliderTarget/M21-SL-3003.SLDPRT

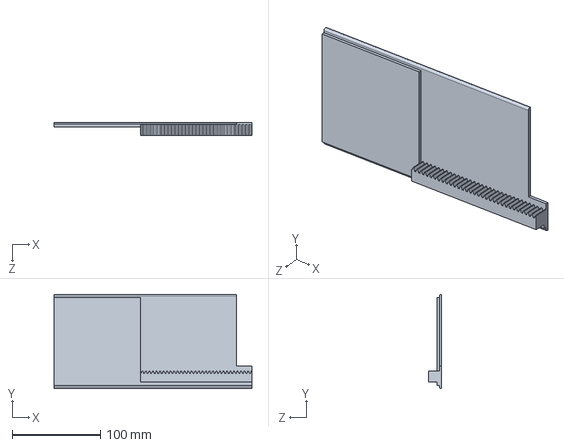
[picture p103: CAD file, 2021-10-06]
cad/DoorSliderTarget/M21-SL-3003.SLDPRT
224.1 x 106.7 x 15.2 mm
