VCHSRobots/EpicFMS/cad/MovingTarget/M21-MT-3006.SLDPRT

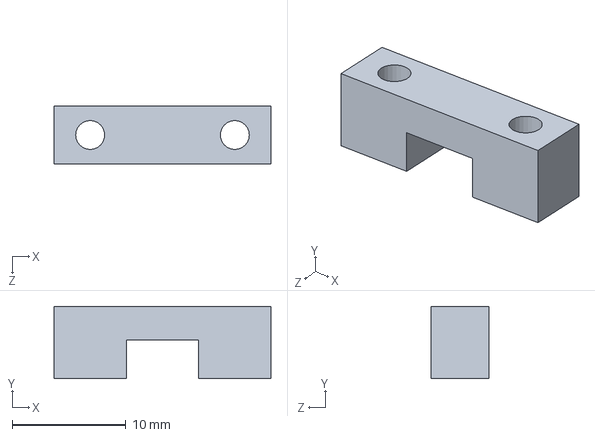
[picture p104: CAD file, 2021-10-06]
cad/MovingTarget/M21-MT-3006.SLDPRT
19.1 x 6.35 x 5.08 mm
