VCHSRobots/EpicFMS/cad/SupplierLib/LipoBattery_1500mah_2S__Amazon.SLDPRT

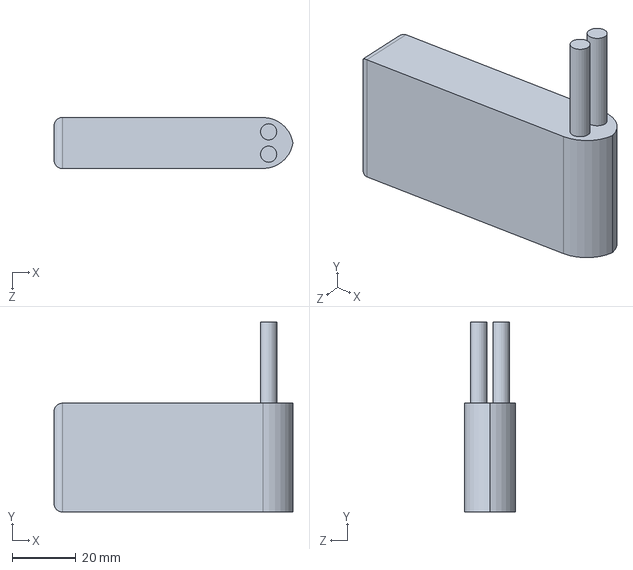
[picture p105: CAD file, 2021-10-06]
cad/SupplierLib/LipoBattery_1500mah_2S__Amazon.SLDPRT
74.8 x 59.4 x 16.0 mm
