VCHSRobots/EpicFMS/cad/DoorSliderTarget/M21-SL-3001.SLDPRT

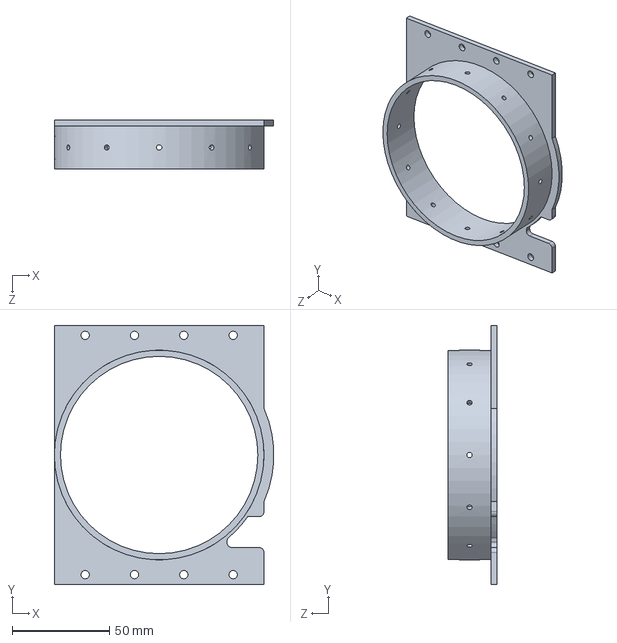
[picture p106: CAD file, 2021-10-06]
cad/DoorSliderTarget/M21-SL-3001.SLDPRT
112.9 x 133.4 x 25.4 mm
