VCHSRobots/EpicFMS/cad/MovingTarget/M21-SL-7001.SLDPRT

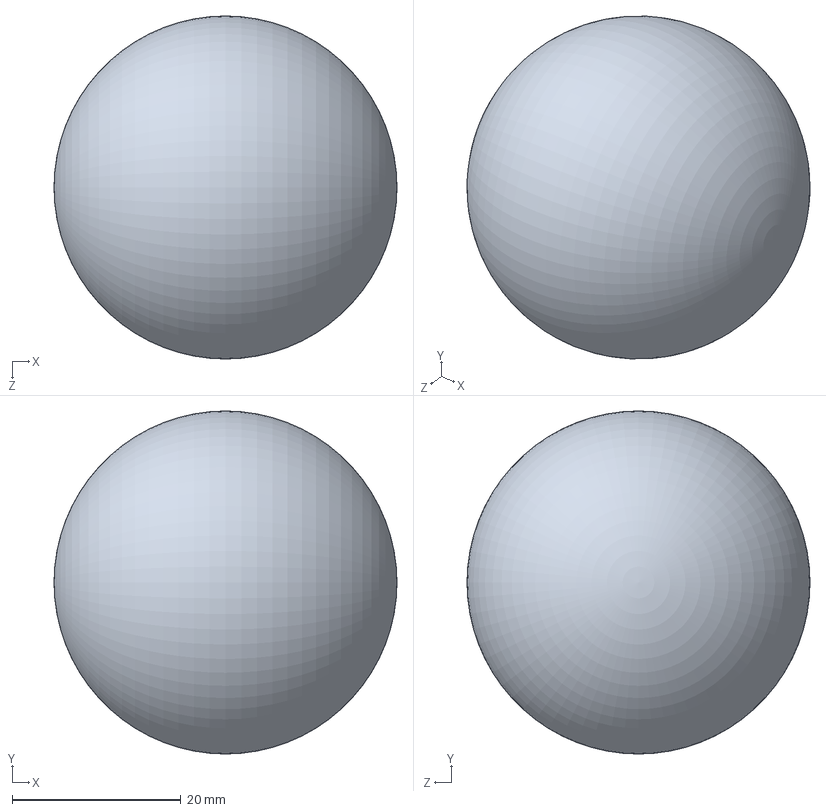
[picture p107: CAD file, 2021-10-06]
cad/MovingTarget/M21-SL-7001.SLDPRT
40.6 x 40.6 x 40.6 mm
