VCHSRobots/EpicFMS/cad/SupplierLib/ESP8266.SLDPRT

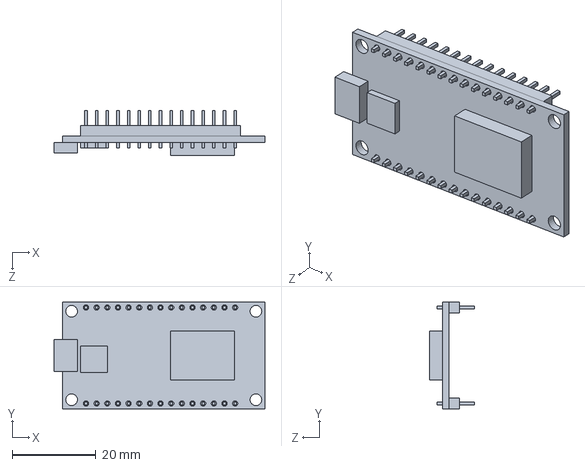
[picture p108: CAD file, 2021-10-06]
cad/SupplierLib/ESP8266.SLDPRT
50.3 x 25.4 x 10.7 mm
