VCHSRobots/EpicFMS/cad/DoorSliderTarget/M21-SL-3005.SLDPRT

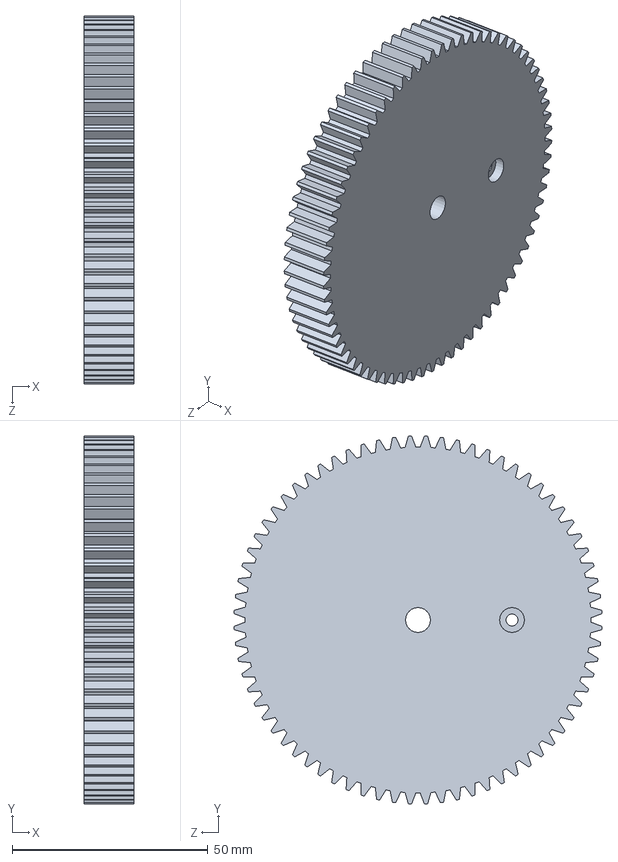
[picture p109: CAD file, 2021-10-06]
cad/DoorSliderTarget/M21-SL-3005.SLDPRT
12.7 x 93.9 x 93.9 mm
