VCHSRobots/EpicFMS/cad/SupplierLib/NeopixelRingSLDPRT.SLDPRT

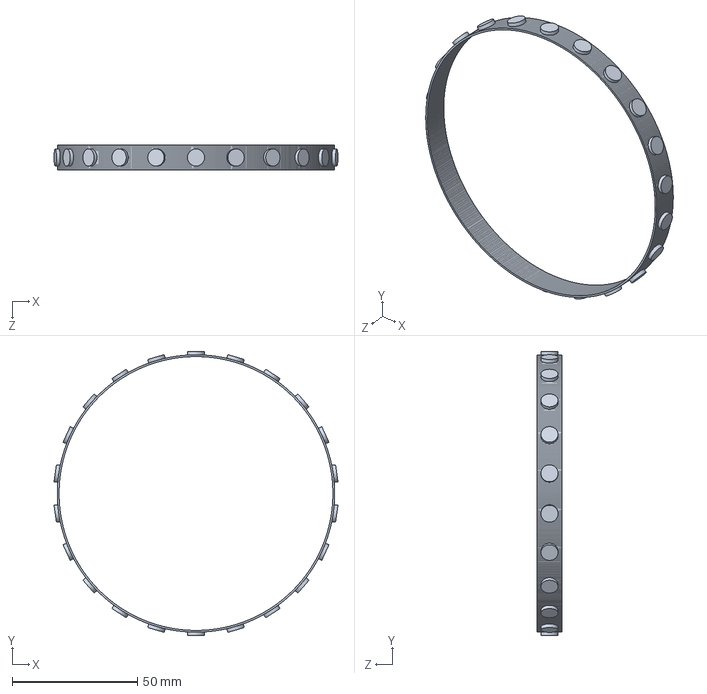
[picture p110: CAD file, 2021-10-06]
cad/SupplierLib/NeopixelRingSLDPRT.SLDPRT
113.3 x 113.4 x 10.2 mm
