VCHSRobots/EpicFMS/cad/SupplierLib/ElegooBoard_Thin.SLDPRT

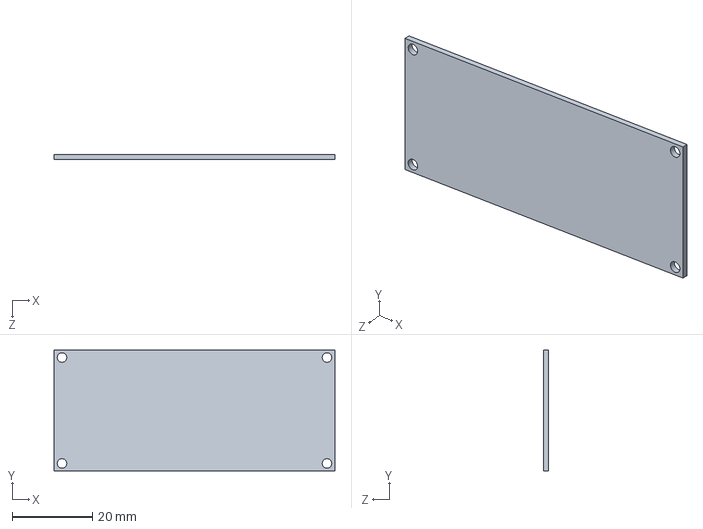
[picture p111: CAD file, 2021-10-06]
cad/SupplierLib/ElegooBoard_Thin.SLDPRT
70.0 x 30.0 x 1.27 mm
