VCHSRobots/EpicFMS/cad/MovingTarget/M21-MT-3007.SLDPRT

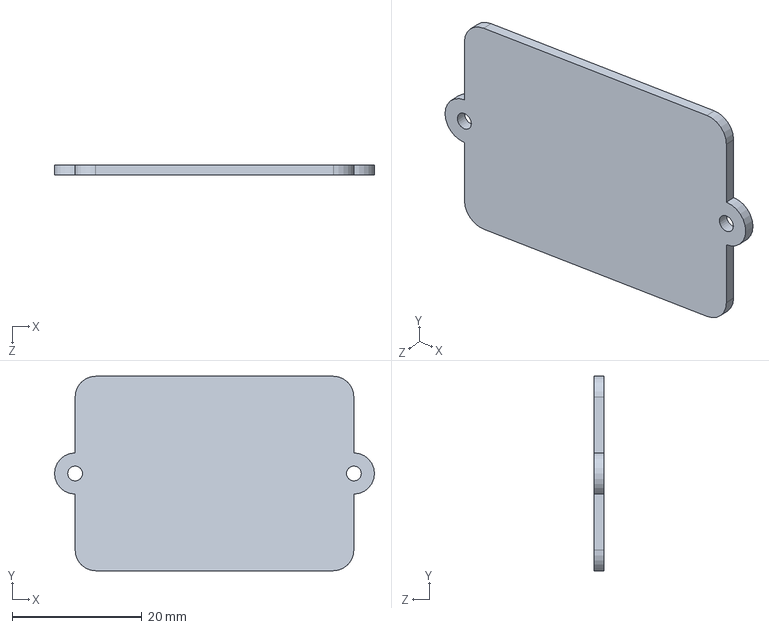
[picture p112: CAD file, 2021-10-06]
cad/MovingTarget/M21-MT-3007.SLDPRT
49.3 x 30.0 x 1.52 mm
