VCHSRobots/EpicFMS/cad/SupplierLib/MicroPushButton.SLDPRT

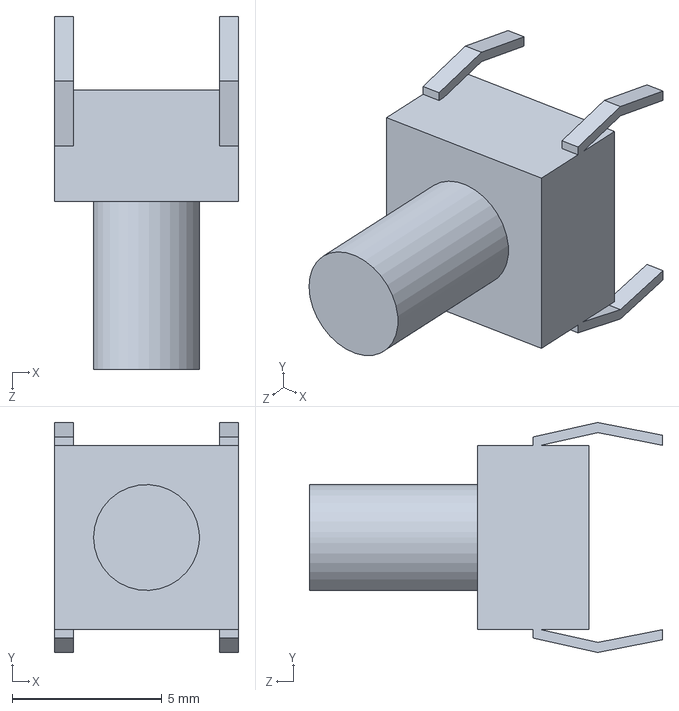
[picture p113: CAD file, 2021-10-06]
cad/SupplierLib/MicroPushButton.SLDPRT
6.15 x 7.67 x 11.8 mm
