VCHSRobots/EpicFMS/cad/MovingTarget/M21-MT-7002.SLDPRT

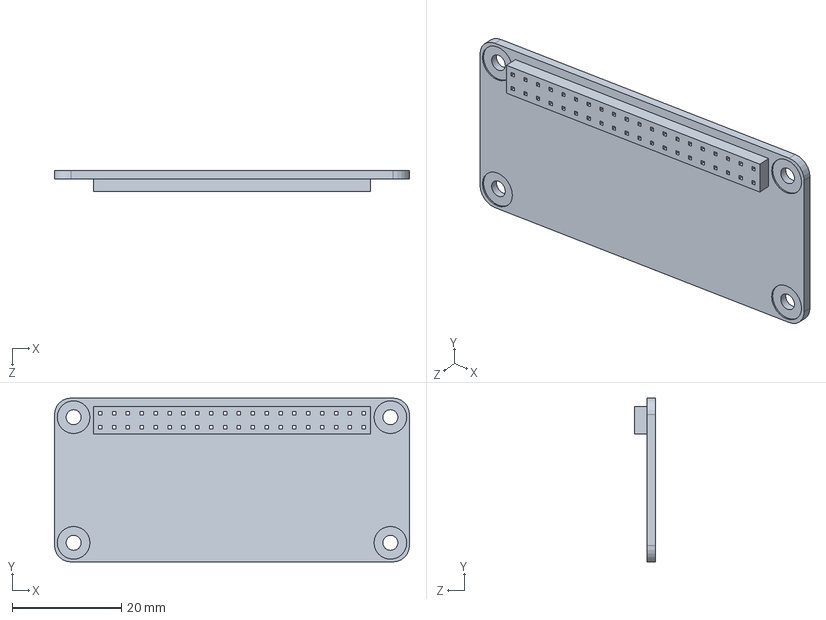
[picture p114: CAD file, 2021-10-06]
cad/MovingTarget/M21-MT-7002.SLDPRT
65.0 x 30.0 x 3.81 mm
