VCHSRobots/EpicFMS/cad/SupplierLib/RockerSwitch.SLDPRT

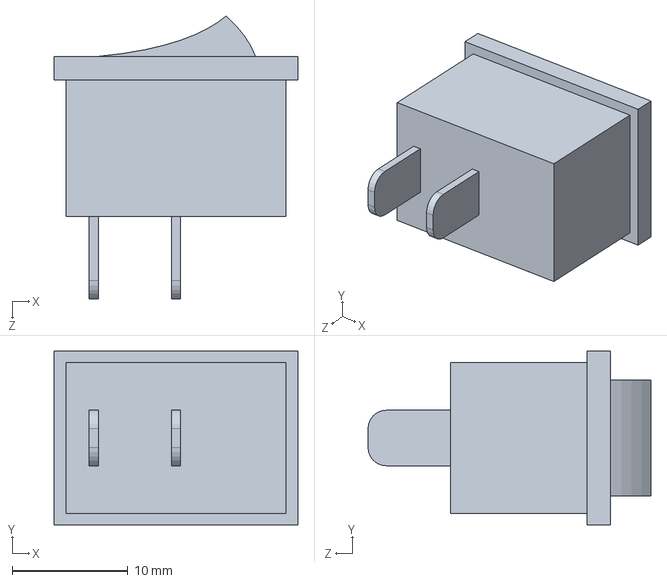
[picture p115: CAD file, 2021-10-06]
cad/SupplierLib/RockerSwitch.SLDPRT
21.0 x 15.0 x 24.4 mm
