VCHSRobots/EpicFMS/cad/MovingTarget/M21-MT-3002.SLDPRT

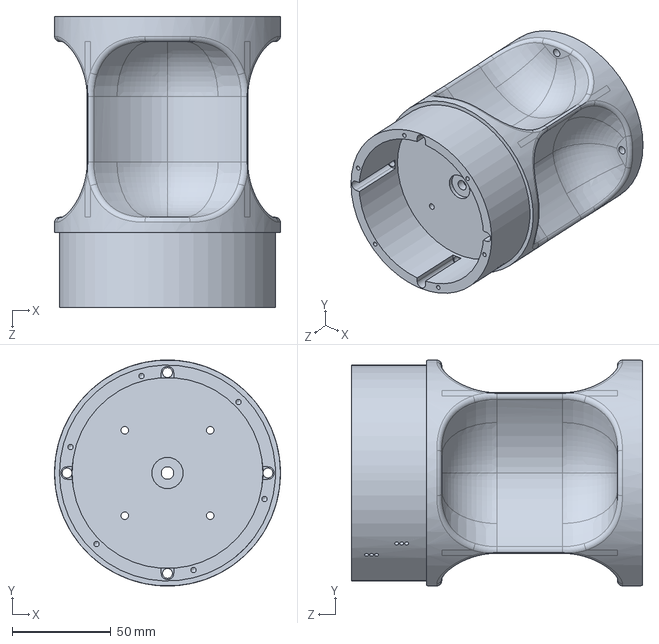
[picture p116: CAD file, 2021-10-06]
cad/MovingTarget/M21-MT-3002.SLDPRT
114.4 x 114.3 x 147.3 mm
