VCHSRobots/EpicFMS/cad/SupplierLib/LipoBattery_2500mah_2S_FatShart_Amazon.SLDPRT

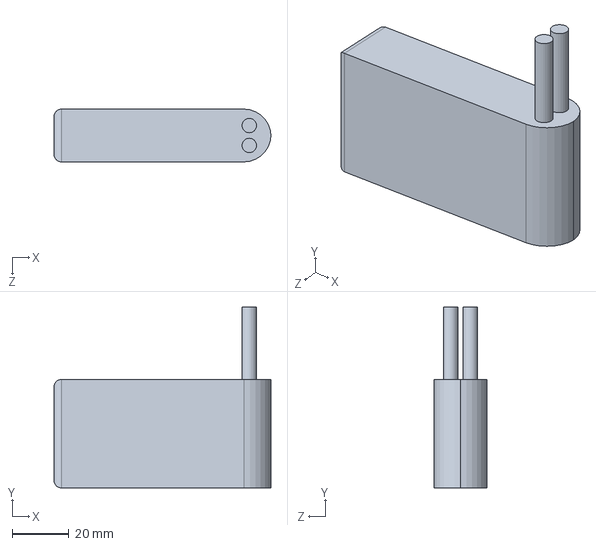
[picture p117: CAD file, 2021-10-06]
cad/SupplierLib/LipoBattery_2500mah_2S_FatShart_Amazon.SLDPRT
76.2 x 63.5 x 18.5 mm
