VCHSRobots/EpicFMS/cad/SupplierLib/HornFor_ZOSKAY_25K_Servo.SLDPRT

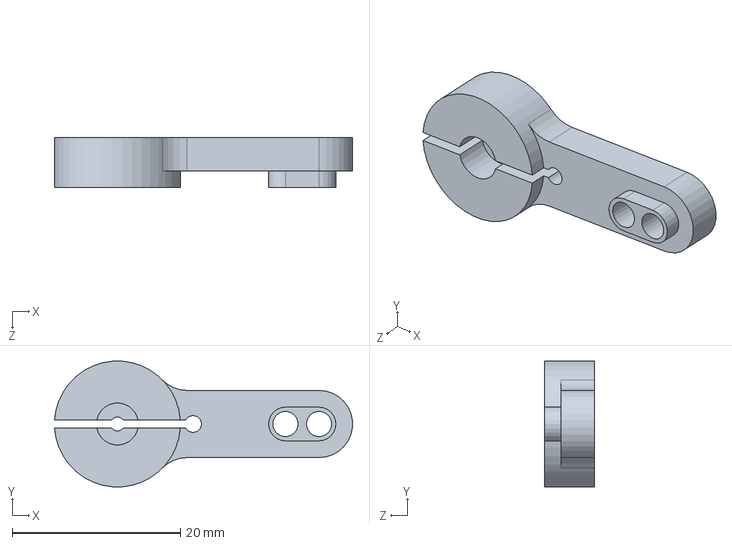
[picture p118: CAD file, 2021-10-06]
cad/SupplierLib/HornFor_ZOSKAY_25K_Servo.SLDPRT
35.5 x 15.0 x 6.00 mm
