VCHSRobots/EpicFMS/cad/SupplierLib/RaspberryPiZero.SLDPRT

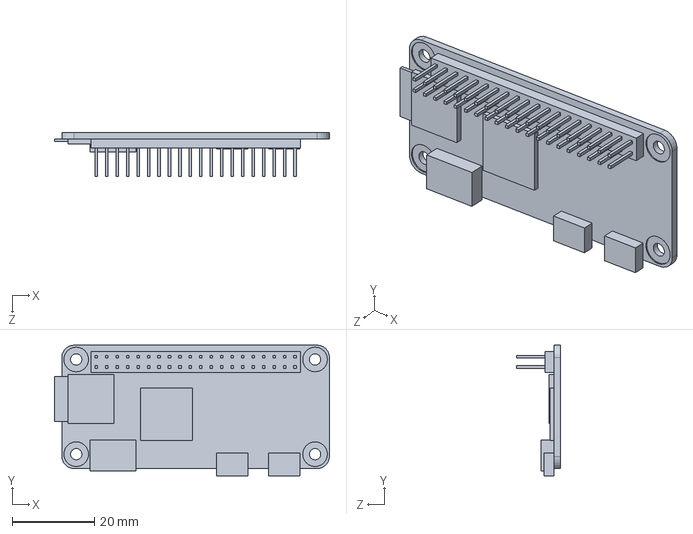
[picture p119: CAD file, 2021-10-06]
cad/SupplierLib/RaspberryPiZero.SLDPRT
66.8 x 31.8 x 10.7 mm
