VCHSRobots/EpicFMS/cad/SupplierLib/ZOSKAY_25K_Servo.SLDPRT

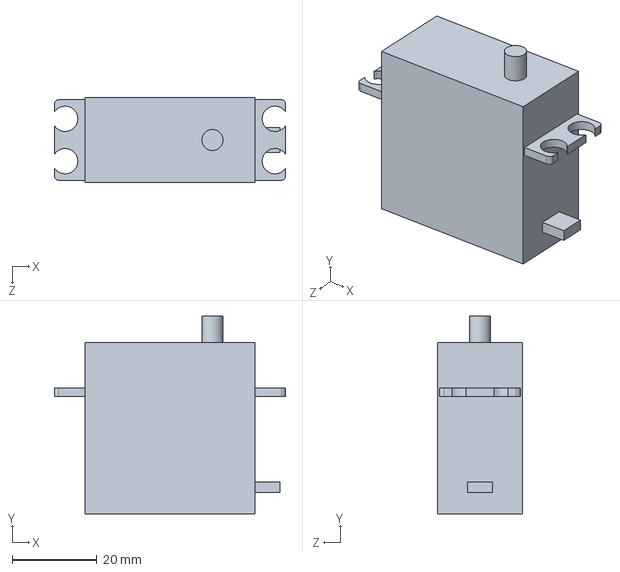
[picture p120: CAD file, 2021-10-06]
cad/SupplierLib/ZOSKAY_25K_Servo.SLDPRT
54.5 x 46.6 x 20.0 mm
