VCHSRobots/EpicFMS/cad/SupplierLib/PanelMountFuse.SLDPRT

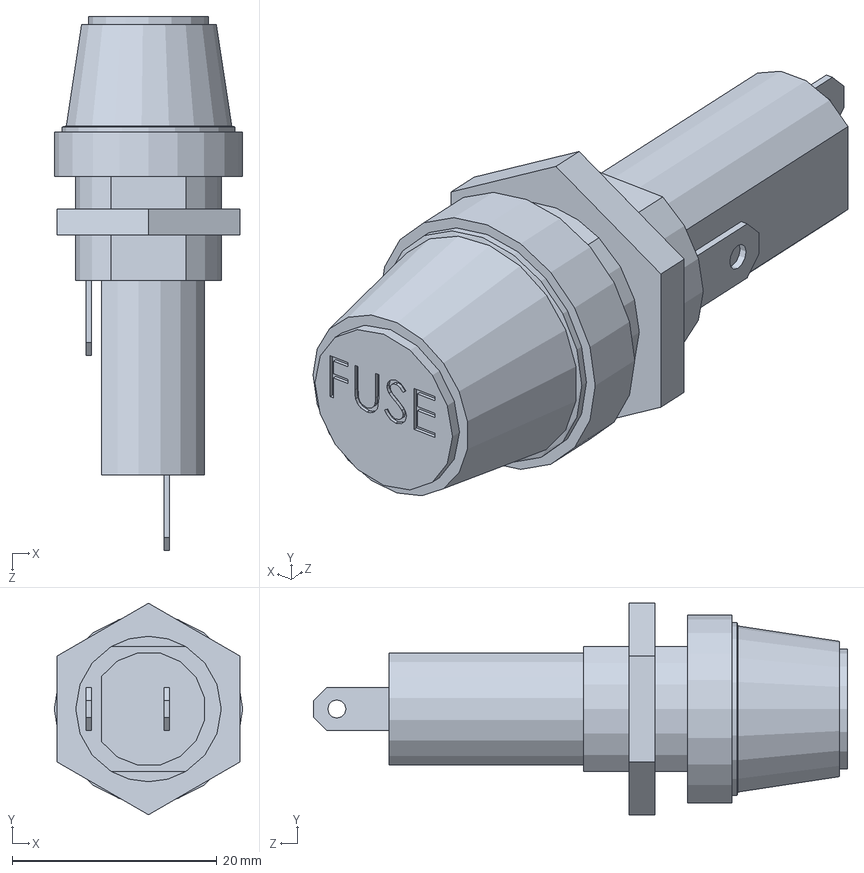
[picture p121: CAD file, 2021-10-05]
cad/SupplierLib/PanelMountFuse.SLDPRT
18.4 x 20.7 x 52.2 mm
