VCHSRobots/EpicFMS/cad/SupplierLib/SmallRockerSwitch.SLDPRT

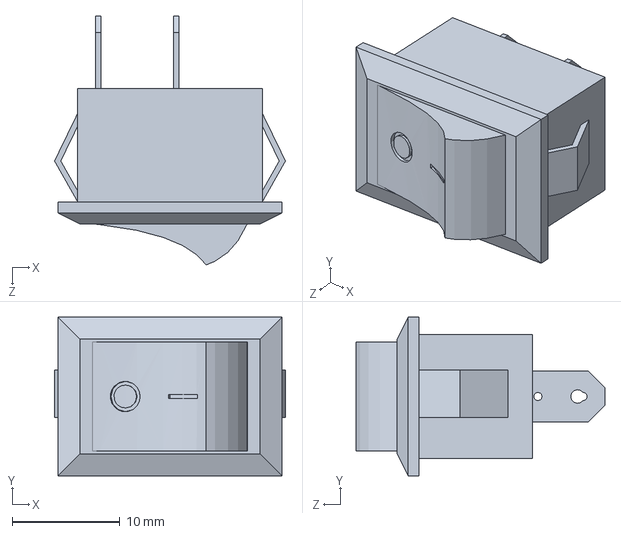
[picture p122: CAD file, 2021-10-05]
cad/SupplierLib/SmallRockerSwitch.SLDPRT
21.5 x 14.7 x 23.1 mm
