VCHSRobots/EpicFMS/esp/Low_Goal_lights_V3/Low_Goal_Lights_V2.ino

#include <Adafruit_NeoPixel.h>
#define LED_PIN1    5
#define LED_PIN2    4
#define LED_COUNT1 12
#define LED_COUNT2 12
#define INPUT_BUTTON 10

//define all constants for events
#define MODE_ERROR 1
#define MODE_NOT_READY 2
#define MODE_STANDBY 3
#define MODE_COUNTDOWN 4
#define MODE_AUTO_MODE 5
#define MODE_SCORE 6
#define MODE_TELEOP 7
#define MODE_END_GAME 8
#define MODE_GAMEOVER 9

char lineout[100];
long timer = millis();
int iled1 = 0;
int iled2 = 0;
long errorCondition = 0;
int dance = 0;
int brightness = 150;
int reverse_lights = 0;

Adafruit_NeoPixel strip1(LED_COUNT1, LED_PIN1, NEO_GRB + NEO_KHZ800);
Adafruit_NeoPixel strip2(LED_COUNT2, LED_PIN2, NEO_GRB + NEO_KHZ800);

void setup() {
  strip1.begin();           // INITIALIZE NeoPixel strip object (REQUIRED)
  strip1.show();            // Turn OFF all pixels ASAP
  strip1.setBrightness(brightness); // Set BRIGHTNESS to about 1/5 (max = 255)
  strip2.begin();           // INITIALIZE NeoPixel strip object (REQUIRED)
  strip2.show();            // Turn OFF all pixels ASAP
  strip2.setBrightness(brightness); // Set BRIGHTNESS to about 1/5 (max = 255)
  pinMode(INPUT_BUTTON, INPUT_PULLUP);
}

void set_all_pixels1(int r, int g, int b){
  for(int i=0; i<12; i++){
  strip1.setPixelColor(i,strip1.Color(r, g, b));
  strip1.show();
  }
 strip1.show();
 strip1.setBrightness(brightness);
}

void set_all_pixels2(int r, int g, int b){
  for(int i=0; i<12; i++){
  strip2.setPixelColor(i,strip1.Color(r, g, b));
  strip2.show();
  }
 strip2.show();
 strip2.setBrightness(brightness);
}
//all events

void led_error(){
strip1.setBrightness(150);
 strip2.setBrightness(150);
    if (millis() - timer <= 500) return; 
   timer = millis();
   if (errorCondition == 0){
    errorCondition = 1;
    set_all_pixels1(0, 0, 255);
    set_all_pixels2(255, 0, 0);
   }
   else{
    set_all_pixels1(255, 0, 0);
    set_all_pixels2(0, 0, 255);
    errorCondition = 0;
   }
}

void led_not_ready(){
 strip1.setBrightness(150);
 strip2.setBrightness(150);
   if (millis() - timer >= 50){
    timer = millis();
    set_all_pixels1(0, 0, 0);
    set_all_pixels2(0, 0, 0);
    strip1.show();
    strip2.show();
    iled1++;
     if (iled1 >= LED_COUNT1){
      iled1 = 0;
     }
     if (iled2 >= LED_COUNT2){
      iled2 = 0;
     }
     strip1.setPixelColor(iled1,strip1.Color(255, 0, 0));
     strip2.setPixelColor(iled1,strip2.Color(255, 0, 0));
     strip1.show();
     strip2.show();
 }
}

void led_standby(){
strip1.setBrightness(150);
 strip2.setBrightness(150);
   if (millis() - timer >= 50){
    timer = millis();
    set_all_pixels1(0, 0, 0);
    set_all_pixels2(0, 0, 0);
    strip1.show();
    strip2.show();
    iled1++;
     if (iled1 >= LED_COUNT1){
      iled1 = 0;
     }
     if (iled2 >= LED_COUNT2){
      iled2 = 0;
     }
     strip1.setPixelColor(iled1,strip1.Color(0, 255, 0));
     strip2.setPixelColor(iled1,strip2.Color(0, 255, 0));
     strip1.show();
     strip2.show();
 }
}

void led_countdown(){
 strip1.setBrightness(150);
 strip2.setBrightness(150);
   if (millis() - timer <=1000){
     set_all_pixels1(255, 0, 0);
     set_all_pixels2(255, 0, 0);
     strip1.show();
     strip2.show();
   }
   if (millis() - timer <=2000){
    if (millis() - timer >1000){
     set_all_pixels1(255, 255, 0);
     set_all_pixels2(155, 255, 0);
     strip1.show();
     strip2.show();
   }
  }
   if (millis() - timer <=3000){
    if (millis() - timer >2000){
     set_all_pixels1(0, 0, 255);
     set_all_pixels2(0, 0, 255);
     strip1.show();
     strip2.show();
   }
  }
     if (millis() - timer <=4000){
    if (millis() - timer >3000){
     set_all_pixels1(0, 255, 0);
     set_all_pixels2(0, 255, 0);
     strip1.show();
     strip2.show();
   }
  }
}

void led_auto_mode(){
 strip1.setBrightness(150);
 strip2.setBrightness(150);
if (millis() - timer <= 500) return; 
   timer = millis();
   if (dance == 0){
    dance = 1;
    set_all_pixels1(0, 255, 0);
    set_all_pixels2(252, 15, 192);
   }
   else{
    set_all_pixels1(252, 15, 192);
    set_all_pixels2(0, 255, 0);
    dance = 0;
   }
}

void led_score(){
  strip1.setBrightness(150);
 strip2.setBrightness(150);
 set_all_pixels1(255, 255, 255);
 set_all_pixels2(155, 255, 255);
 strip1.show();
 strip2.show();
}

void led_teleop(){
strip1.setBrightness(150);
 strip2.setBrightness(150);
     if (millis() - timer >= 50){
    timer = millis();
    set_all_pixels1(0, 0, 0);
    set_all_pixels2(0, 0, 0);
    strip1.show();
    strip2.show();
    iled1++;
     if (iled1 >= LED_COUNT1){
      iled1 = 0;
     }
     if (iled2 >= LED_COUNT2){
      iled2 = 0;
     }
     strip1.setPixelColor(iled1,strip1.Color(0, 0, 255));
     strip2.setPixelColor(iled1,strip2.Color(0, 0, 255));
     strip1.show();
     strip2.show();
 }
}

void led_end_game(){
 strip1.setBrightness(150);
 strip2.setBrightness(150);
       if (millis() - timer <= 100) return; 
   timer = millis();
   if (dance == 0){
    dance = 1;
    set_all_pixels1(random(), random(), random());
    set_all_pixels2(random(), random(), random());
   }
   else{
    set_all_pixels1(random(), random(), random());
    set_all_pixels2(random(), random(), random());
    dance = 0;
   } 
}

void led_gameover(){
  set_all_pixels1( 0, 255, 0);
  set_all_pixels2( 0, 255, 0);
  if (millis()-timer >=2){
   if (reverse_lights == 0) brightness--;
   if (reverse_lights == 1) brightness++;
   if (brightness >=100) reverse_lights = 0;
   if (brightness <= 0) reverse_lights = 1;
  }
}

//The calling of events to lights
void led_manager(int mode){
 switch(mode){
    case MODE_ERROR: led_error(); break;
    case MODE_NOT_READY: led_not_ready(); break;
    case MODE_STANDBY: led_standby(); break;
    case MODE_COUNTDOWN: led_countdown(); break;
    case MODE_AUTO_MODE: led_auto_mode(); break;
    case MODE_SCORE: led_score(); break;
    case MODE_TELEOP: led_teleop(); break;
    case MODE_END_GAME: led_end_game(); break;
    case MODE_GAMEOVER: led_gameover(); break;
 }
}

//The following is test code

void loop(){
   if(digitalRead(INPUT_BUTTON) == HIGH){
    led_manager(MODE_ERROR);
   }else{
    led_manager(MODE_GAMEOVER);
   }
}
