VCHSRobots/EpicFMS/esp/gtdevice/debug.ino

void show_pins() {
  sprintf(lineout, "Pin D0 = GPI0 %d", digitalPinToInterrupt(D0)); Serial.println(lineout);
  sprintf(lineout, "Pin D1 = GPI0 %d", digitalPinToInterrupt(D1)); Serial.println(lineout);
  sprintf(lineout, "Pin D2 = GPI0 %d", digitalPinToInterrupt(D2)); Serial.println(lineout);
  sprintf(lineout, "Pin D3 = GPI0 %d", digitalPinToInterrupt(D3)); Serial.println(lineout);
  sprintf(lineout, "Pin D4 = GPI0 %d", digitalPinToInterrupt(D4)); Serial.println(lineout);
  sprintf(lineout, "Pin D5 = GPI0 %d", digitalPinToInterrupt(D5)); Serial.println(lineout);
  sprintf(lineout, "Pin D6 = GPI0 %d", digitalPinToInterrupt(D6)); Serial.println(lineout);
  sprintf(lineout, "Pin D7 = GPI0 %d", digitalPinToInterrupt(D7)); Serial.println(lineout);
  sprintf(lineout, "Pin D8 = GPI0 %d", digitalPinToInterrupt(D8)); Serial.println(lineout);
  sprintf(lineout, "Pin D9 = GPI0 %d", digitalPinToInterrupt(D9)); Serial.println(lineout);
  sprintf(lineout, "Pin D10 = GPI0 %d", digitalPinToInterrupt(D10)); Serial.println(lineout);

  //sprintf(lineout, "Pin D11 = GPI0 %d", digitalPinToInterrupt(D11)); Serial.println(lineout);
  //sprintf(lineout, "Pin D12 = GPI0 %d", digitalPinToInterrupt(D12)); Serial.println(lineout);
  //sprintf(lineout, "Pin D13 = GPI0 %d", digitalPinToInterrupt(D13)); Serial.println(lineout);
  //sprintf(lineout, "Pin D14 = GPI0 %d", digitalPinToInterrupt(D14)); Serial.println(lineout);
  //sprintf(lineout, "Pin D15 = GPI0 %d", digitalPinToInterrupt(D15)); Serial.println(lineout);
  //sprintf(lineout, "Pin D16 = GPI0 %d", digitalPinToInterrupt(D16)); Serial.println(lineout);
  //sprintf(lineout, "Pin D17 = GPI0 %d", digitalPinToInterrupt(D17)); Serial.println(lineout);
}
